AHSolidSnake/F-14A-Cockpit/Panels/Left Outboard/Back Spacer.stl

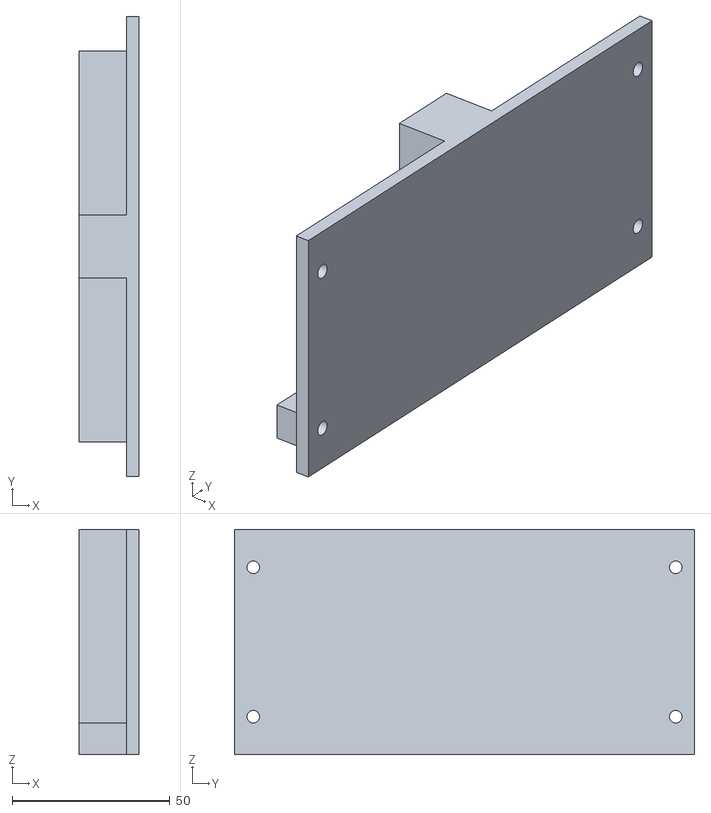
[picture p28: CAD file, 2025-07-25]
Panels/Left Outboard/Back Spacer.stl
19.0 x 146.0 x 71.4
