AHSolidSnake/F-14A-Cockpit/Panels/Left Outboard/ICS/ICS - Top Panel - Light.stl

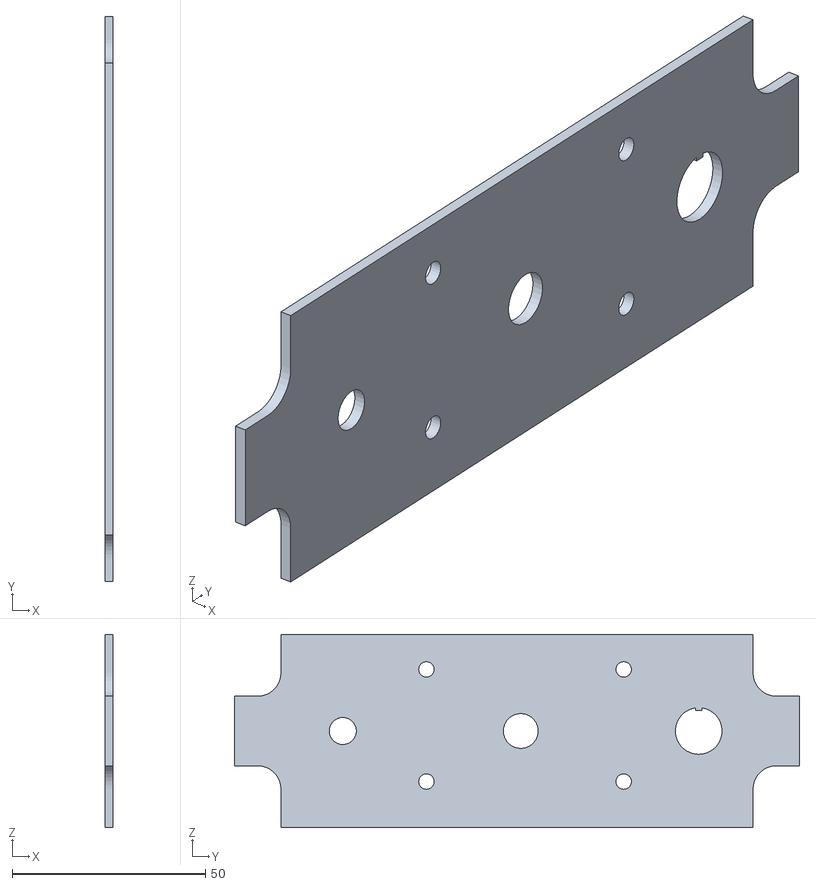
[picture p29: CAD file, 2025-02-26]
Panels/Left Outboard/ICS/ICS - Top Panel - Light.stl
2.00 x 146.1 x 50.0
