AHSolidSnake/F-14A-Cockpit/Panels/Left Outboard/THROTTLE/THROTTLE - Top Panel - Engrave.stl

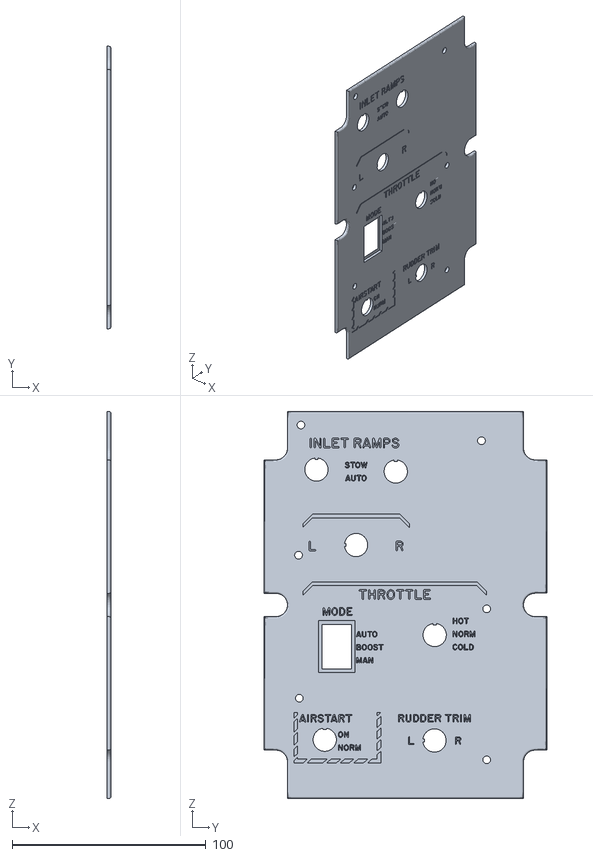
[picture p30: CAD file, 2025-02-26]
Panels/Left Outboard/THROTTLE/THROTTLE - Top Panel - Engrave.stl
2.00 x 146.0 x 200.0
