AHSolidSnake/F-14A-Cockpit/Panels/Left Outboard/VOLUME/VOLUME - Top Panel - Engrave.stl

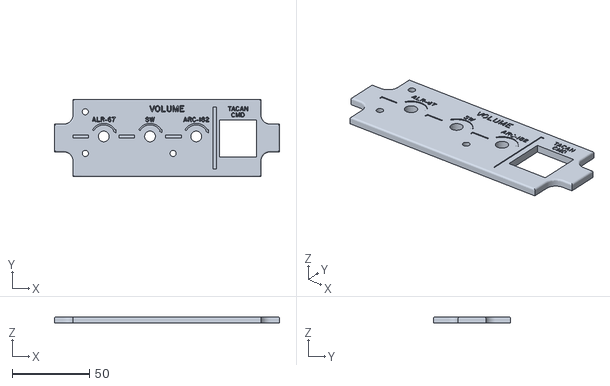
[picture p31: CAD file, 2025-06-24]
Panels/Left Outboard/VOLUME/VOLUME - Top Panel - Engrave.stl
146.0 x 50.0 x 4.00
