AHSolidSnake/F-14A-Cockpit/Panels/Left Vertical Panel/FUEL/FUEL - Top Panel - Light.stl

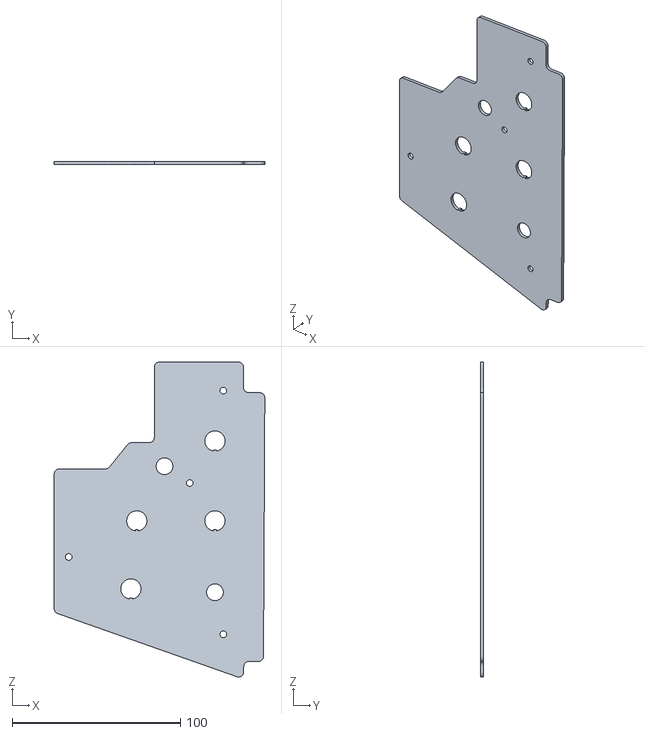
[picture p32: CAD file, 2025-03-23]
Panels/Left Vertical Panel/FUEL/FUEL - Top Panel - Light.stl
125.3 x 2.00 x 187.4
