AHSolidSnake/F-14A-Cockpit/Panels/Left Vertical Panel/GEAR/GEAR - Bottom Panel.stl

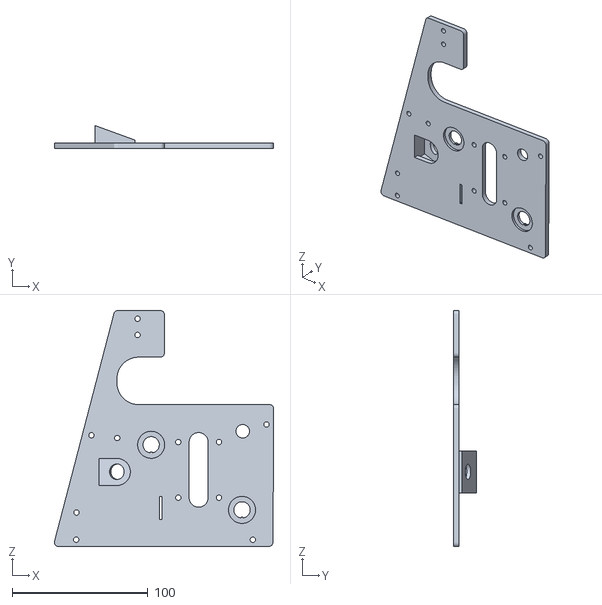
[picture p33: CAD file, 2025-06-24]
Panels/Left Vertical Panel/GEAR/GEAR - Bottom Panel.stl
161.7 x 16.9 x 174.0
