AHSolidSnake/F-14A-Cockpit/Panels/Left Vertical Panel/LAUNCH BAR/LAUNCH BAR - Top Panel - Engrave.stl

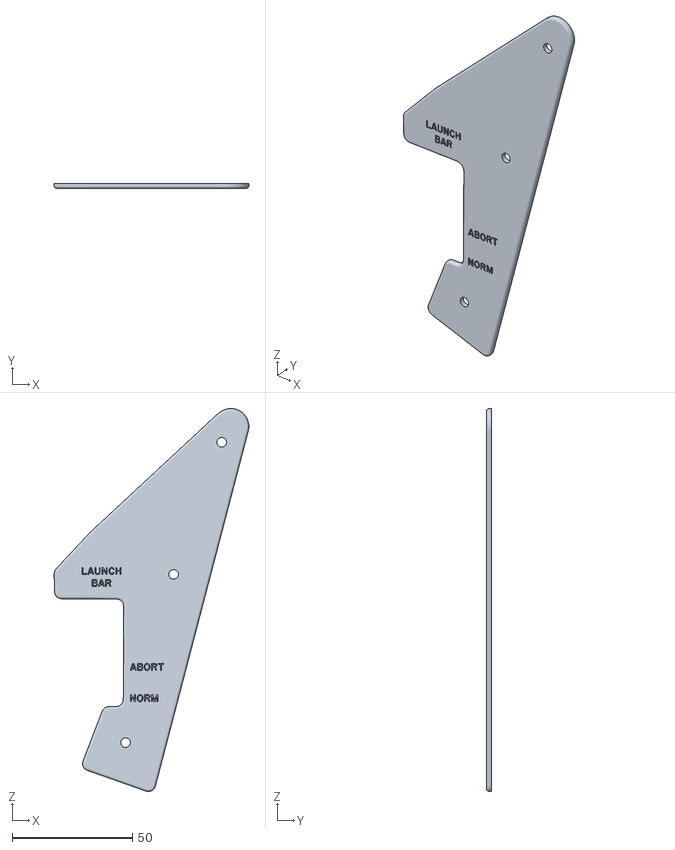
[picture p34: CAD file, 2025-03-22]
Panels/Left Vertical Panel/LAUNCH BAR/LAUNCH BAR - Top Panel - Engrave.stl
81.0 x 2.00 x 159.5
