AHSolidSnake/F-14A-Cockpit/Panels/Left Vertical Panel/LVP - Back Plate.stl

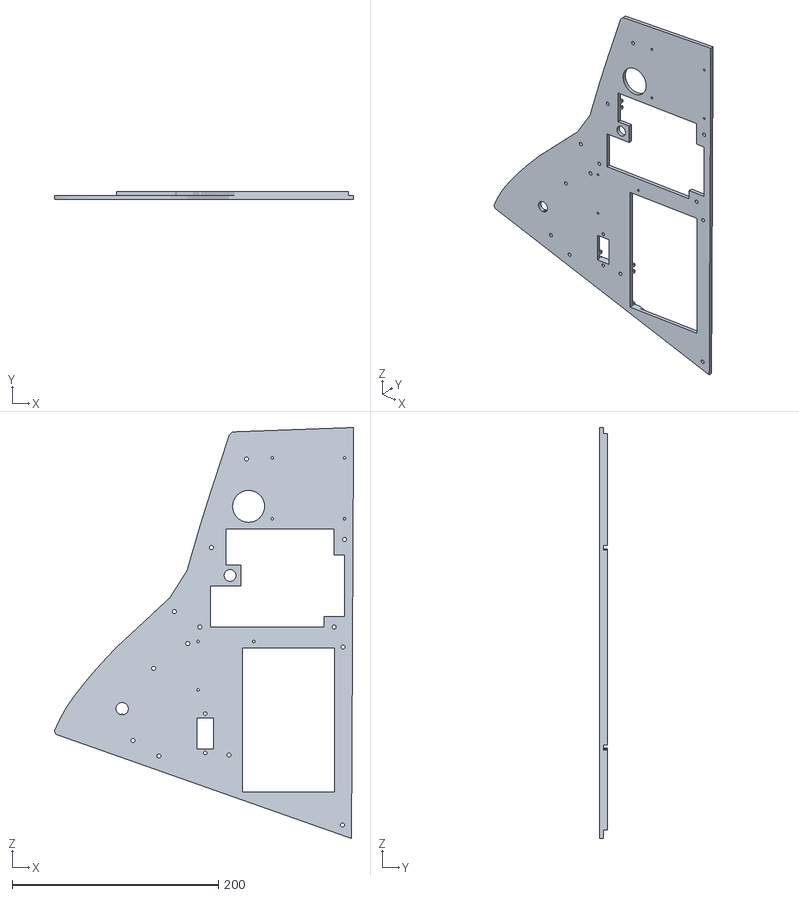
[picture p35: CAD file, 2025-03-16]
Panels/Left Vertical Panel/LVP - Back Plate.stl
290.1 x 8.00 x 398.5
