AHSolidSnake/F-14A-Cockpit/Panels/Right Inboard/AIRCON/AIRCON - Wheel.stl

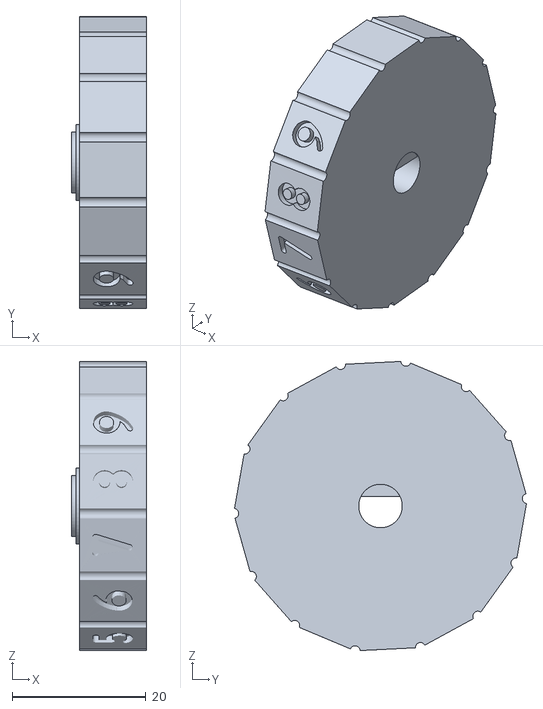
[picture p36: CAD file, 2025-06-24]
Panels/Right Inboard/AIRCON/AIRCON - Wheel.stl
11.2 x 43.7 x 43.3
