AHSolidSnake/F-14A-Cockpit/Panels/Right Inboard/C&W/C&W - Box.stl

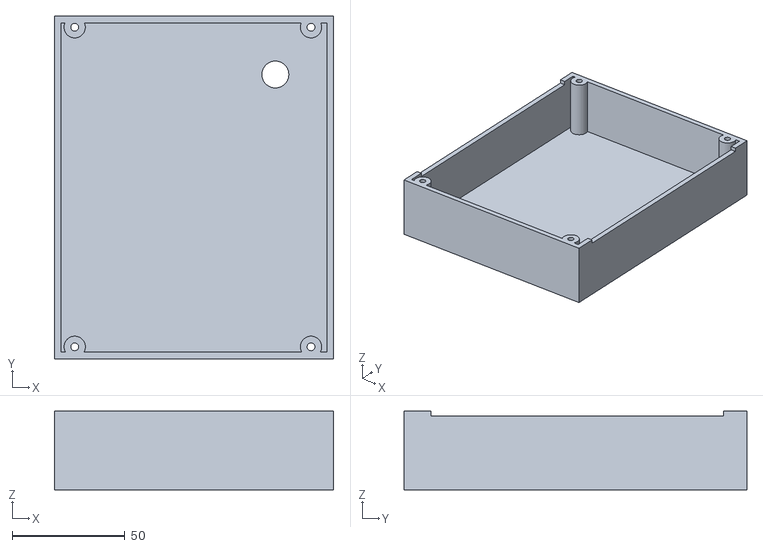
[picture p37: CAD file, 2025-05-10]
Panels/Right Inboard/C&W/C&W - Box.stl
124.0 x 152.4 x 35.0
