AHSolidSnake/F-14A-Cockpit/Panels/Right Inboard/EXTENV/EXTENV - Box.stl

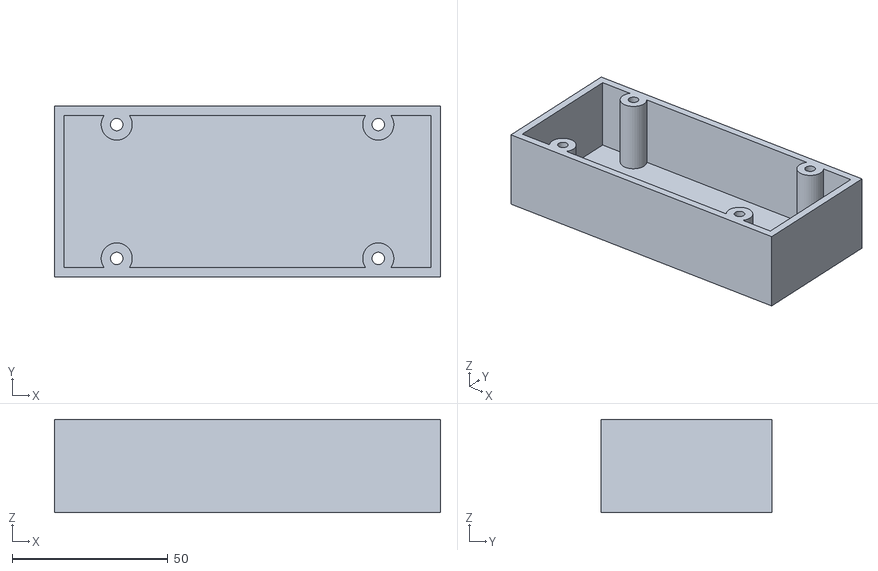
[picture p38: CAD file, 2025-04-17]
Panels/Right Inboard/EXTENV/EXTENV - Box.stl
124.0 x 55.0 x 30.0
