AHSolidSnake/F-14A-Cockpit/Panels/Right Inboard/HYD TRANS/HYD TRANS - Box.stl

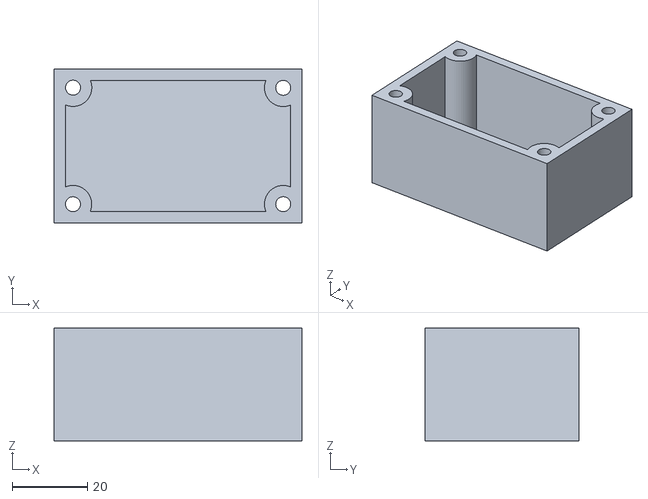
[picture p39: CAD file, 2025-04-17]
Panels/Right Inboard/HYD TRANS/HYD TRANS - Box.stl
66.0 x 41.0 x 30.0
