AHSolidSnake/F-14A-Cockpit/Panels/Right Inboard/MASTERGEN/MASTERGEN - Box.stl

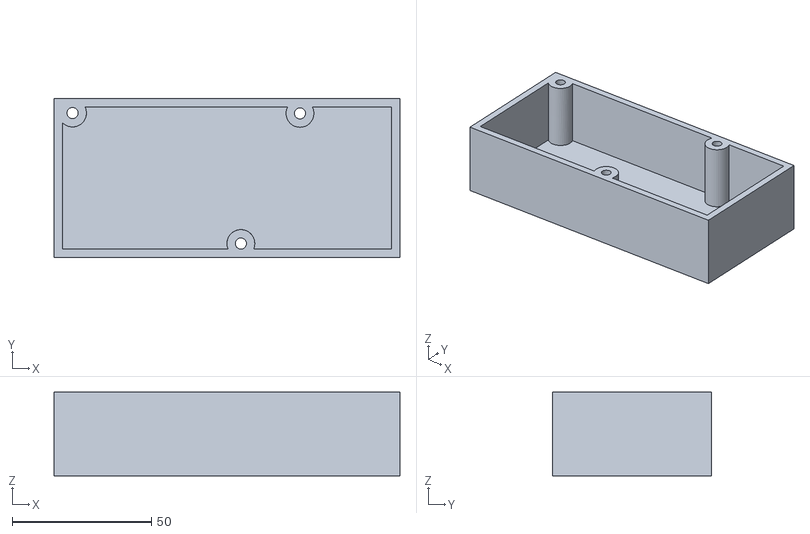
[picture p40: CAD file, 2025-04-17]
Panels/Right Inboard/MASTERGEN/MASTERGEN - Box.stl
124.1 x 57.0 x 30.0
