AHSolidSnake/F-14A-Cockpit/Panels/Right Inboard/SPOILERS/SPOILERS - Box.stl

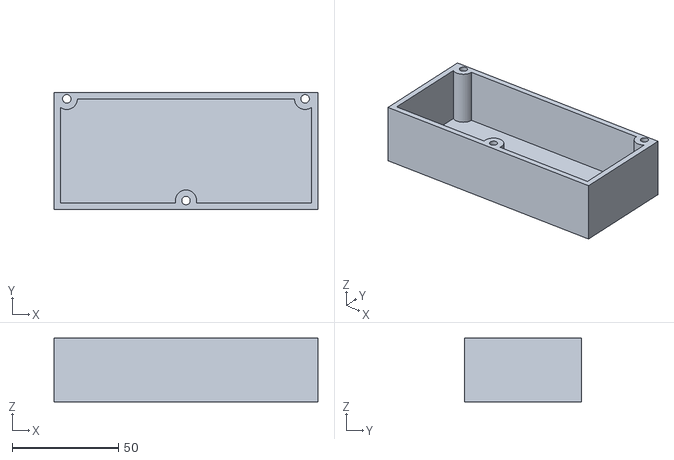
[picture p41: CAD file, 2025-04-13]
Panels/Right Inboard/SPOILERS/SPOILERS - Box.stl
124.1 x 55.0 x 30.0
