AHSolidSnake/F-14A-Cockpit/Panels/Right Instrument Panel/RIP - Back Plate.stl

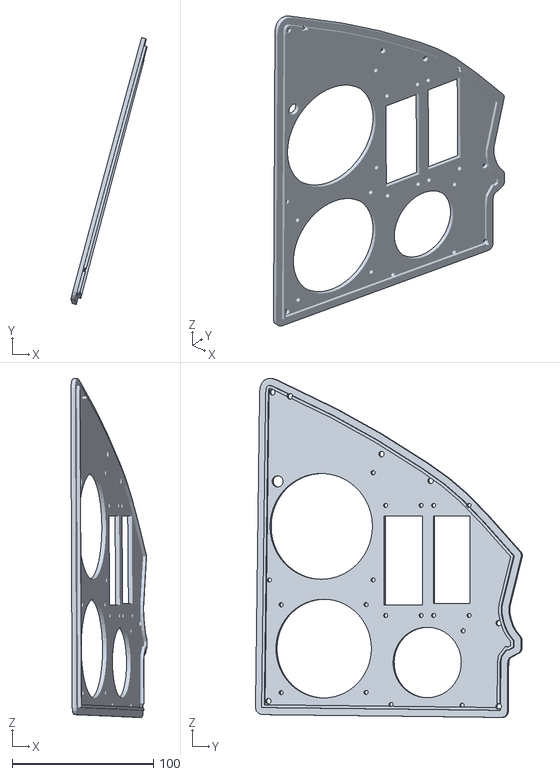
[picture p42: CAD file, 2025-03-30]
Panels/Right Instrument Panel/RIP - Back Plate.stl
54.2 x 189.3 x 240.3
