AHSolidSnake/F-14A-Cockpit/Panels/Right Outboard/COMPASS/COMPASS - Box.stl

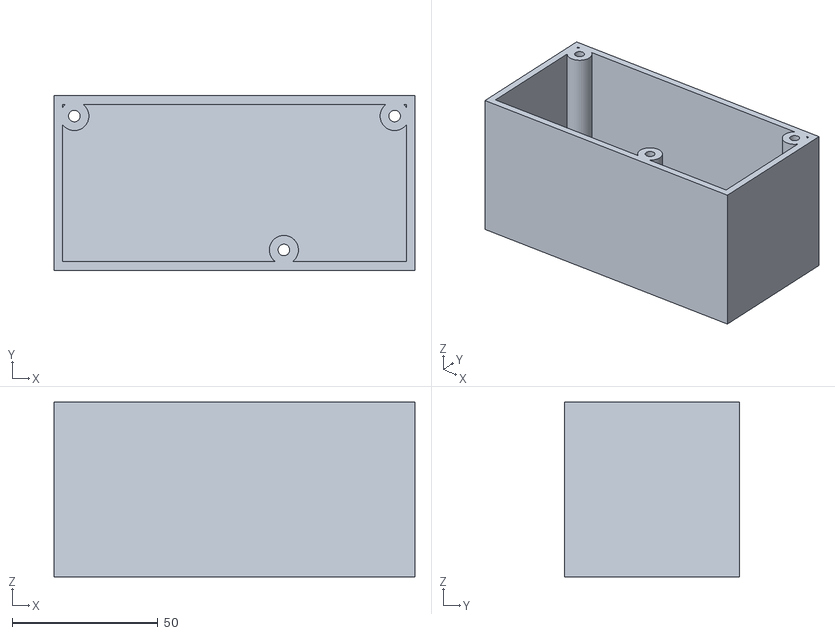
[picture p43: CAD file, 2025-03-30]
Panels/Right Outboard/COMPASS/COMPASS - Box.stl
124.1 x 60.0 x 60.0
