AHSolidSnake/F-14A-Cockpit/Panels/Right Outboard/ILS/ILS - Box.stl

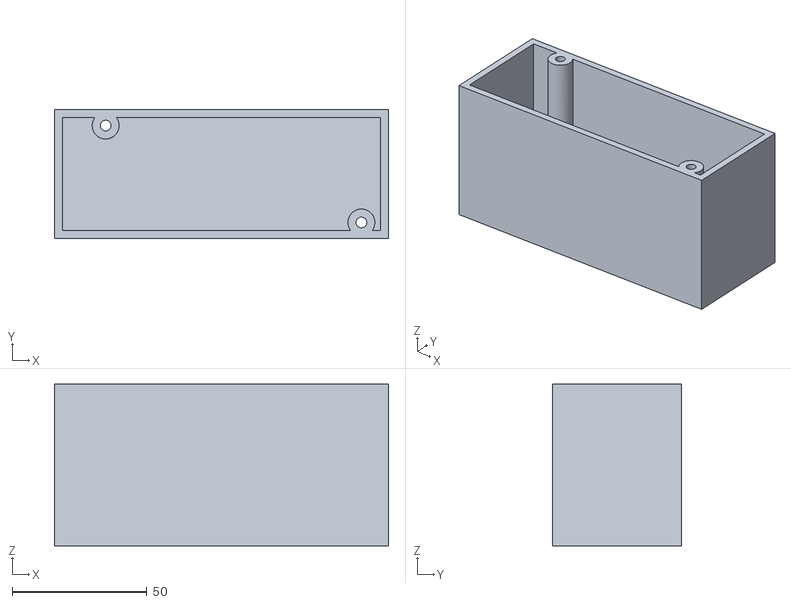
[picture p44: CAD file, 2025-03-30]
Panels/Right Outboard/ILS/ILS - Box.stl
124.1 x 48.0 x 60.0
