AHSolidSnake/F-14A-Cockpit/Panels/Right Outboard/MASTER LIGHTS/MASTER LIGHTS - Bottom Panel.stl

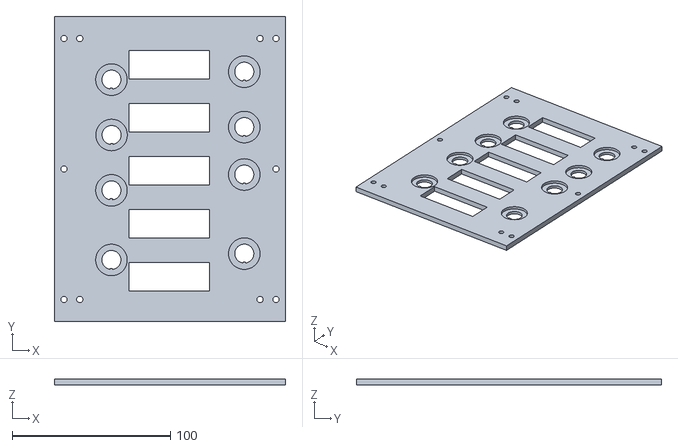
[picture p45: CAD file, 2025-04-11]
Panels/Right Outboard/MASTER LIGHTS/MASTER LIGHTS - Bottom Panel.stl
146.1 x 193.0 x 4.00
