AHSolidSnake/F-14A-Cockpit/Panels/Right Outboard/MASTER TEST/MASTER TEST - Bottom Panel.stl

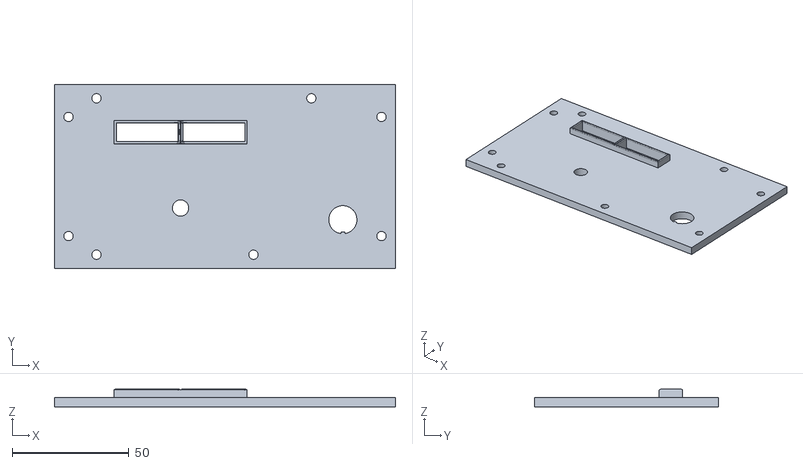
[picture p46: CAD file, 2025-03-30]
Panels/Right Outboard/MASTER TEST/MASTER TEST - Bottom Panel.stl
146.1 x 79.0 x 7.50
