AHSolidSnake/F-14A-Cockpit/Panels/Right Outboard/Spacer-OxygenFlow.stl

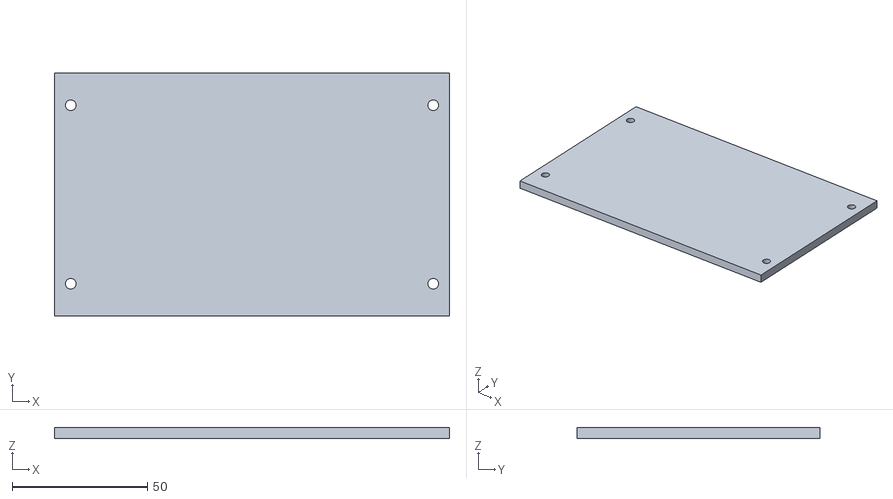
[picture p47: CAD file, 2025-03-22]
Panels/Right Outboard/Spacer-OxygenFlow.stl
146.1 x 90.0 x 4.00
