AHSolidSnake/F-14A-Cockpit/Panels/Right Sidewall/CANOPY/CANOPY - Box.stl

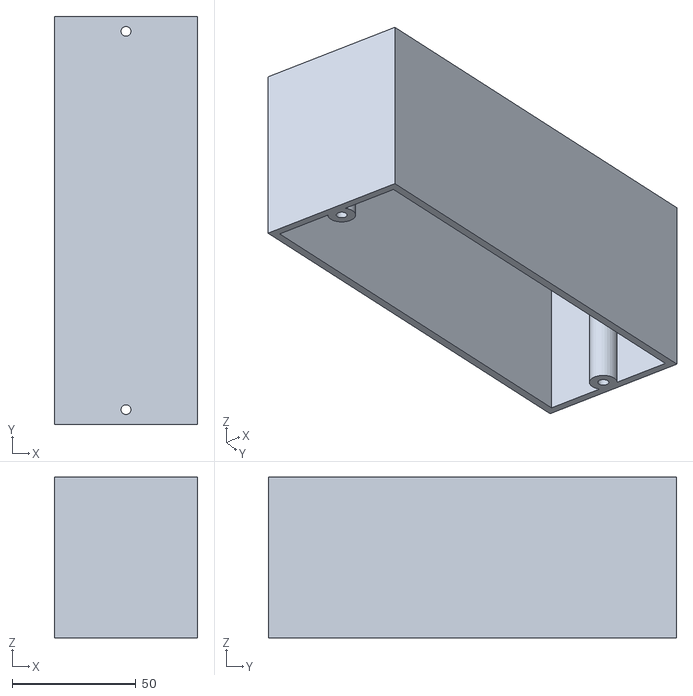
[picture p48: CAD file, 2025-06-24]
Panels/Right Sidewall/CANOPY/CANOPY - Box.stl
58.0 x 165.0 x 65.0
