AHSolidSnake/F-14A-Cockpit/Panels/Right Vertical Panel/HOOK/HOOK - Handle.stl

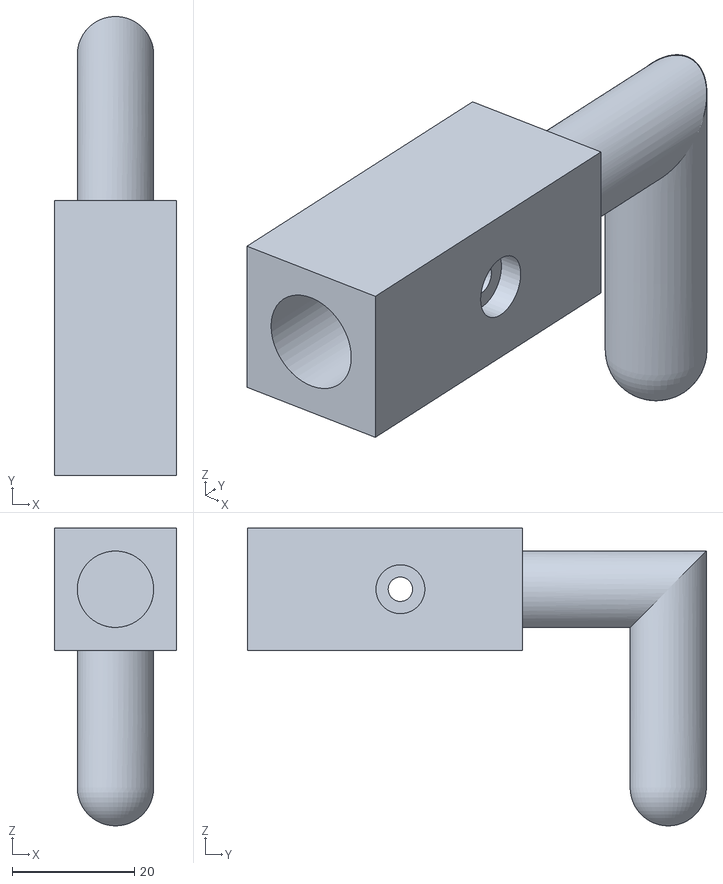
[picture p50: CAD file, 2025-06-24]
Panels/Right Vertical Panel/HOOK/HOOK - Handle.stl
20.0 x 75.0 x 48.7
