AHSolidSnake/F-14A-Cockpit/Panels/Right Vertical Panel/PDCP/PDCP - Top Panel - Engrave.stl

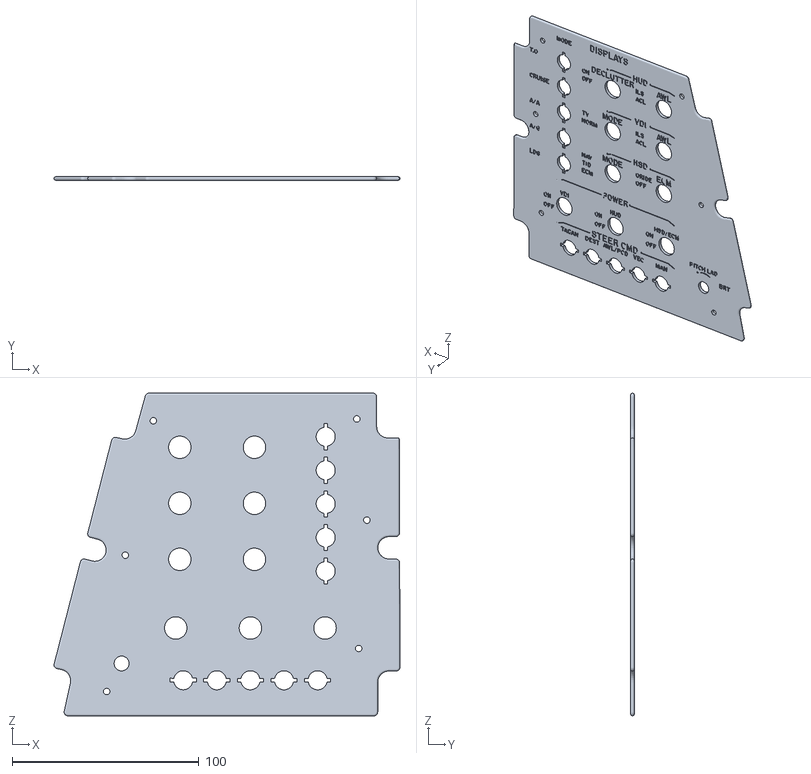
[picture p51: CAD file, 2025-04-07]
Panels/Right Vertical Panel/PDCP/PDCP - Top Panel - Engrave.stl
185.3 x 2.00 x 172.9
