AHSolidSnake/F-14A-Cockpit/Panels/Right Vertical Panel/RVP - Back Plate.stl

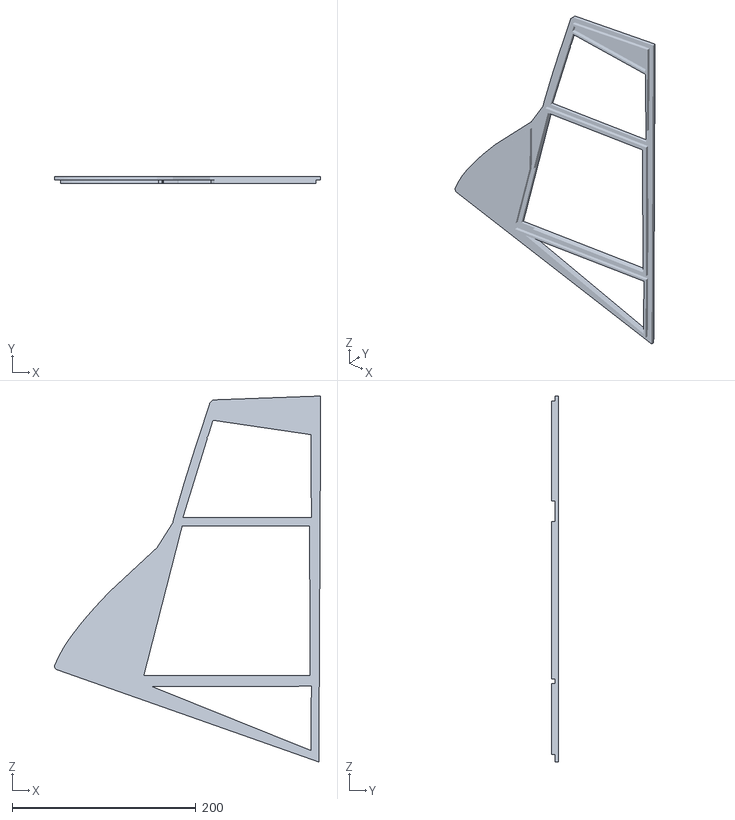
[picture p52: CAD file, 2025-03-15]
Panels/Right Vertical Panel/RVP - Back Plate.stl
290.1 x 8.00 x 398.5
