AHSolidSnake/F-14A-Cockpit/Panels/Support/Center Panel/ACM/ACM - Box - Top Left.stl

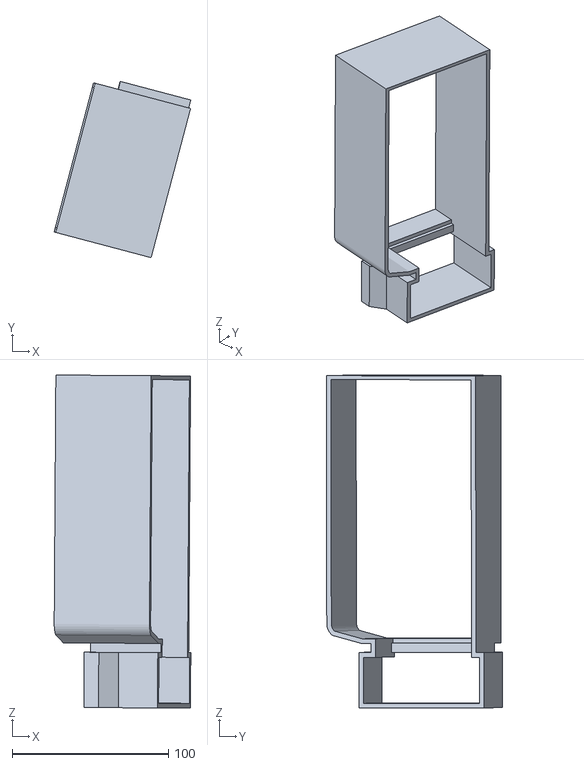
[picture p53: CAD file, 2025-03-09]
Panels/Support/Center Panel/ACM/ACM - Box - Top Left.stl
87.4 x 112.8 x 213.0
