AHSolidSnake/F-14A-Cockpit/Panels/Support/Center Panel/HSD/HSD - Box - Bottom.stl

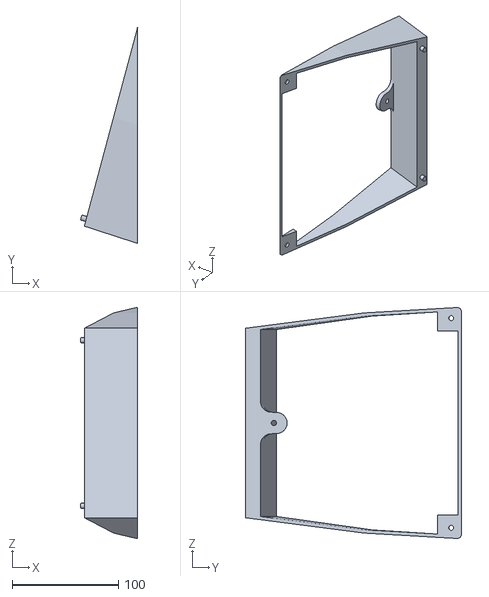
[picture p54: CAD file, 2025-03-30]
Panels/Support/Center Panel/HSD/HSD - Box - Bottom.stl
53.7 x 202.8 x 217.1
