AHSolidSnake/F-14A-Cockpit/Panels/Support/Center Panel/VDI/VDI - Box - Bottom.stl

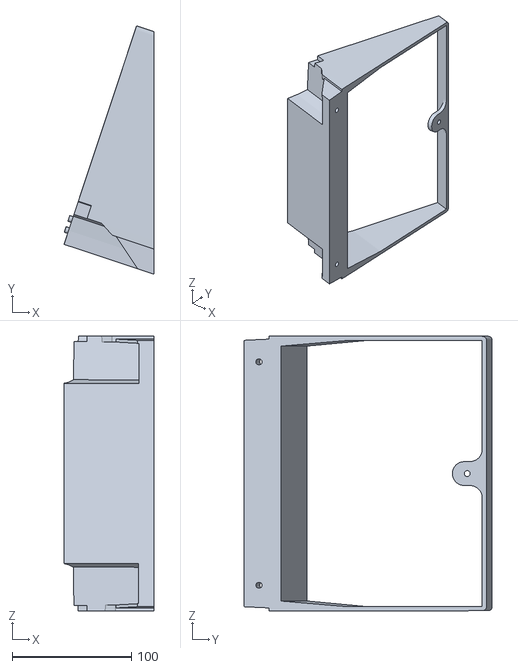
[picture p55: CAD file, 2025-03-29]
Panels/Support/Center Panel/VDI/VDI - Box - Bottom.stl
75.4 x 208.1 x 230.3
