AHSolidSnake/F-14A-Cockpit/Panels/Support/Left Vertical Panel/LVP - Box - Bottom.stl

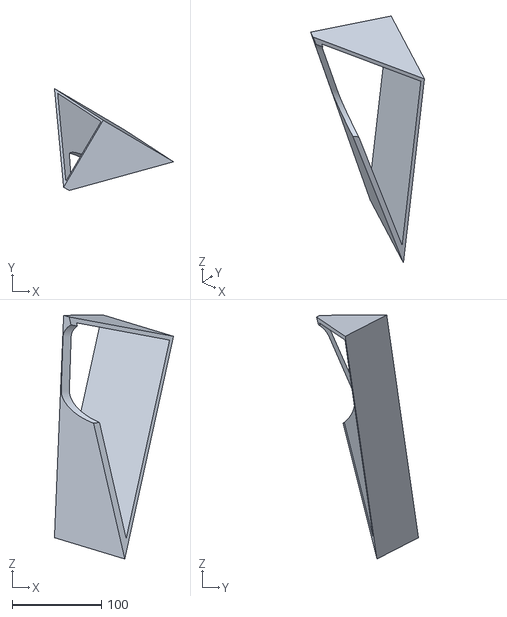
[picture p56: CAD file, 2025-03-30]
Panels/Support/Left Vertical Panel/LVP - Box - Bottom.stl
133.1 x 114.0 x 272.7
