AHSolidSnake/F-14A-Cockpit/Panels/Support/Right Vertical Panel/RVP - Box - Bottom.stl

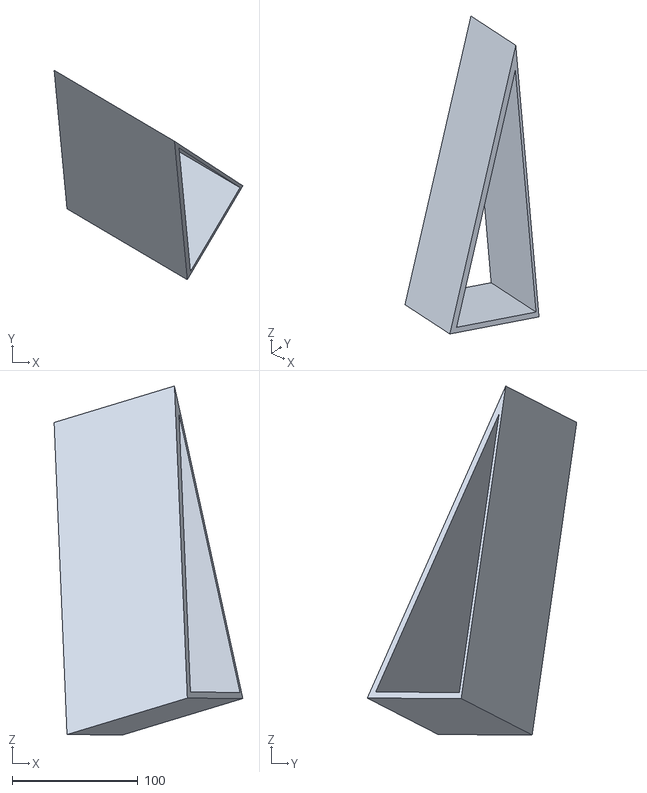
[picture p57: CAD file, 2025-03-30]
Panels/Support/Right Vertical Panel/RVP - Box - Bottom.stl
150.3 x 166.8 x 277.9
