AHSolidSnake/F-14A-Cockpit/Panels/Support/Side Panels/Left Middle Wedge.stl

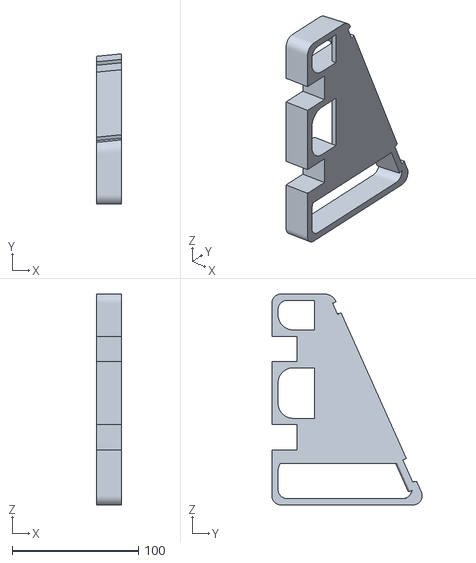
[picture p58: CAD file, 2025-06-24]
Panels/Support/Side Panels/Left Middle Wedge.stl
20.0 x 119.2 x 167.3
