AHSolidSnake/F-14A-Cockpit/Throttle/Base/Box/Back Plate Mount.stl

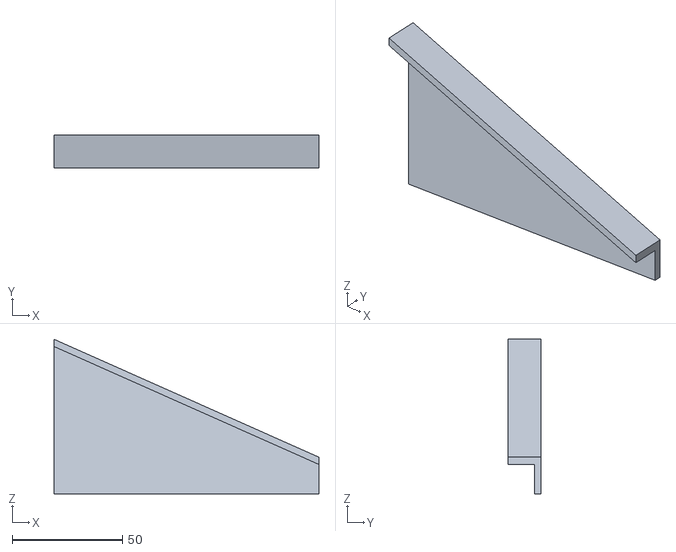
[picture p59: CAD file, 2025-06-24]
Throttle/Base/Box/Back Plate Mount.stl
120.1 x 15.0 x 70.0
