AHSolidSnake/F-14A-Cockpit/Throttle/Base/Flaps/Flaps Pot Mount.stl

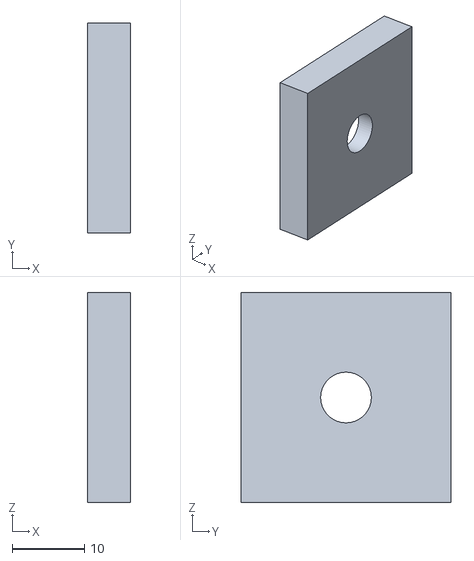
[picture p60: CAD file, 2025-06-24]
Throttle/Base/Flaps/Flaps Pot Mount.stl
6.00 x 29.0 x 29.0
