AHSolidSnake/F-14A-Cockpit/Throttle/Base/Throttle Base/Throttle Levers Left Plate.stl

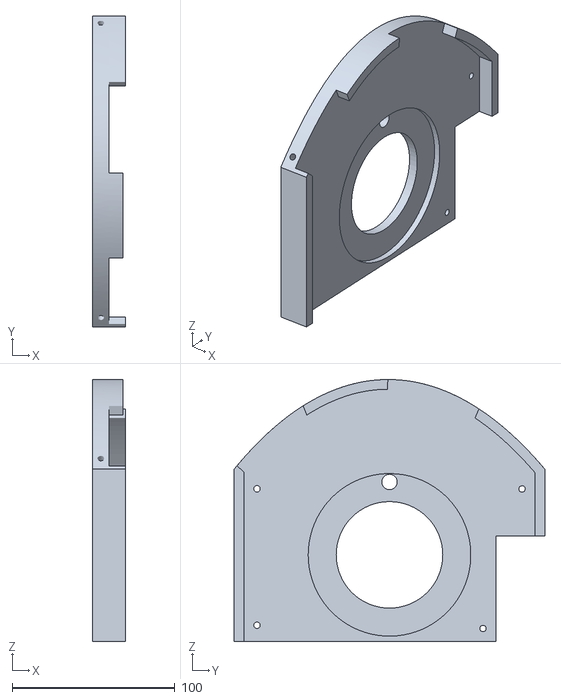
[picture p61: CAD file, 2025-06-24]
Throttle/Base/Throttle Base/Throttle Levers Left Plate.stl
20.0 x 191.0 x 161.1
