AHSolidSnake/F-14A-Cockpit/Throttle/Base/Wing Sweep/Mechanism.stl

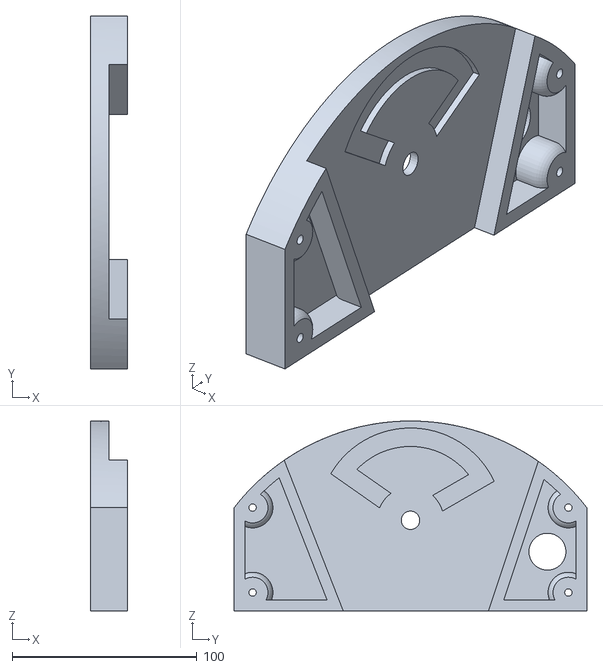
[picture p62: CAD file, 2025-06-24]
Throttle/Base/Wing Sweep/Mechanism.stl
20.0 x 191.0 x 102.9
