AHSolidSnake/F-14A-Cockpit/Throttle/Grips/Levers/Right Arm.stl

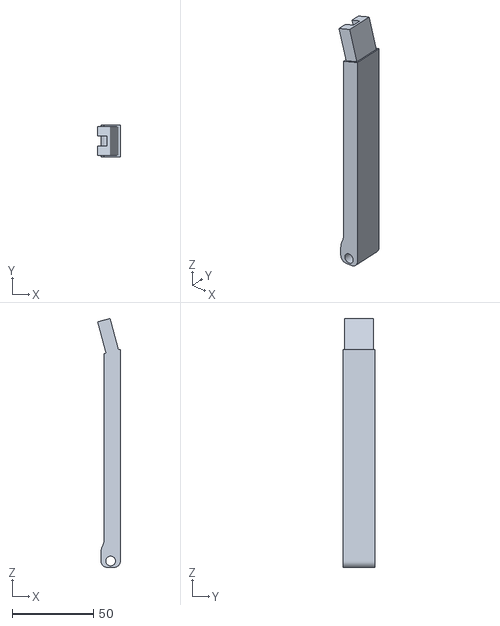
[picture p63: CAD file, 2025-06-24]
Throttle/Grips/Levers/Right Arm.stl
14.1 x 20.0 x 153.7
