AHSolidSnake/F-14A-Cockpit/Extras/Drill Guide.stl

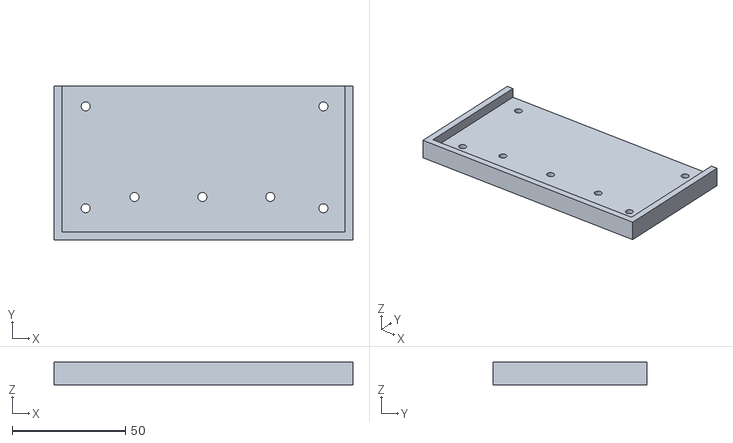
[picture p64: CAD file, 2025-04-07]
Extras/Drill Guide.stl
132.1 x 68.0 x 10.0
