AHSolidSnake/F-14A-Cockpit/Panels/Center Panel/ACM/ACM - AoA/ACM - AoA - Back Plate.stl

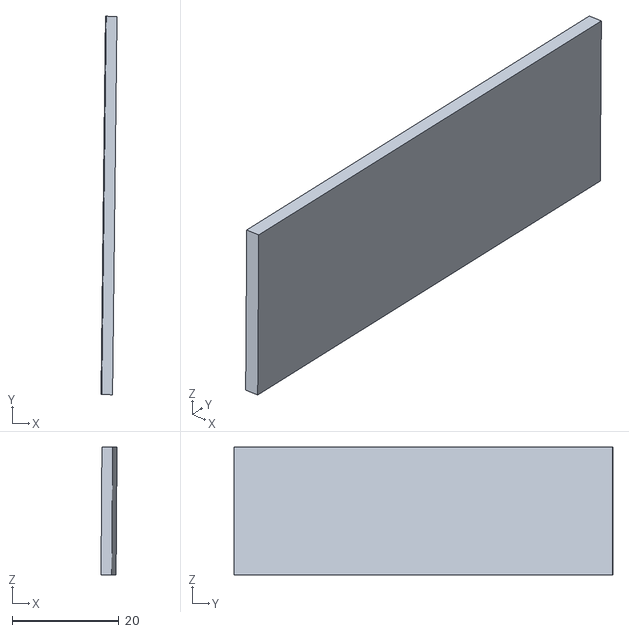
[picture p65: CAD file, 2025-03-23]
Panels/Center Panel/ACM/ACM - AoA/ACM - AoA - Back Plate.stl
3.02 x 71.0 x 24.0
