AHSolidSnake/F-14A-Cockpit/Panels/Center Panel/ACM/ACM - Lights/ACM - Lights - Collision Light.stl

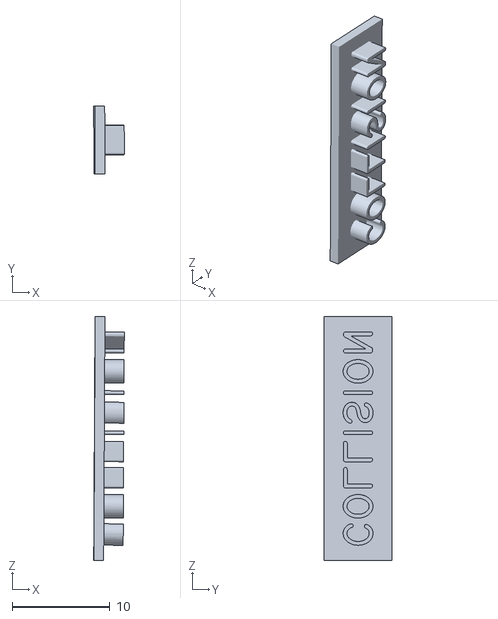
[picture p66: CAD file, 2025-03-16]
Panels/Center Panel/ACM/ACM - Lights/ACM - Lights - Collision Light.stl
3.14 x 7.00 x 25.0
