AHSolidSnake/F-14A-Cockpit/Panels/Center Panel/ACM/ACM - Master Arm - Cover.stl

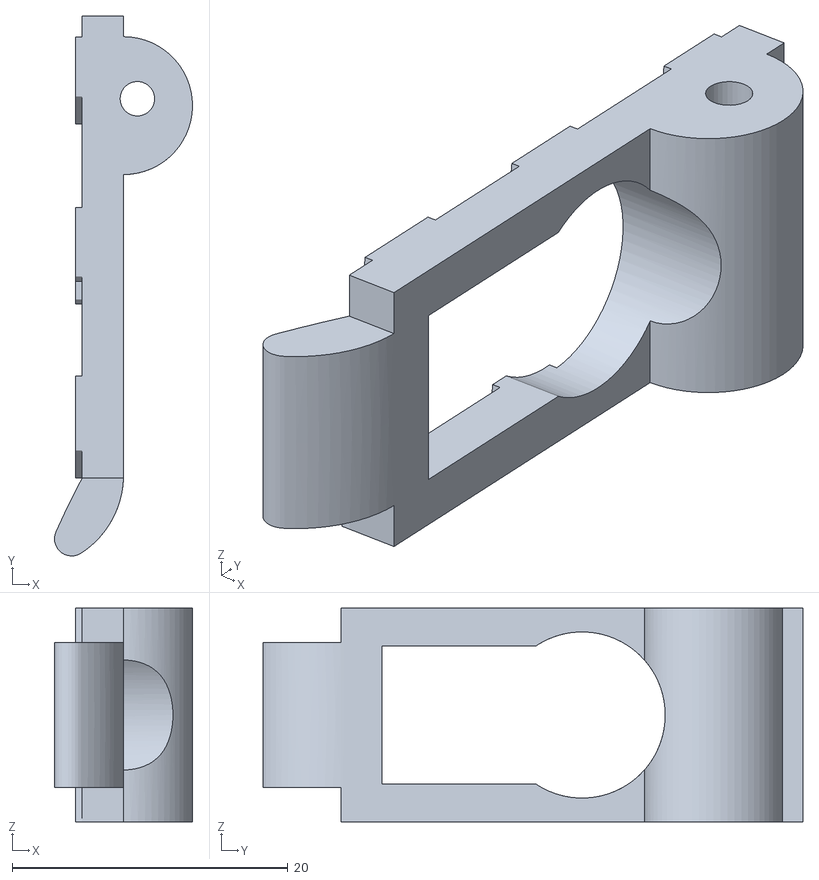
[picture p67: CAD file, 2025-03-16]
Panels/Center Panel/ACM/ACM - Master Arm - Cover.stl
10.0 x 39.2 x 15.5
