AHSolidSnake/F-14A-Cockpit/Panels/Center Panel/ACM/ACM - Turn Slip/ACM - Turn Slip - Engrave.stl

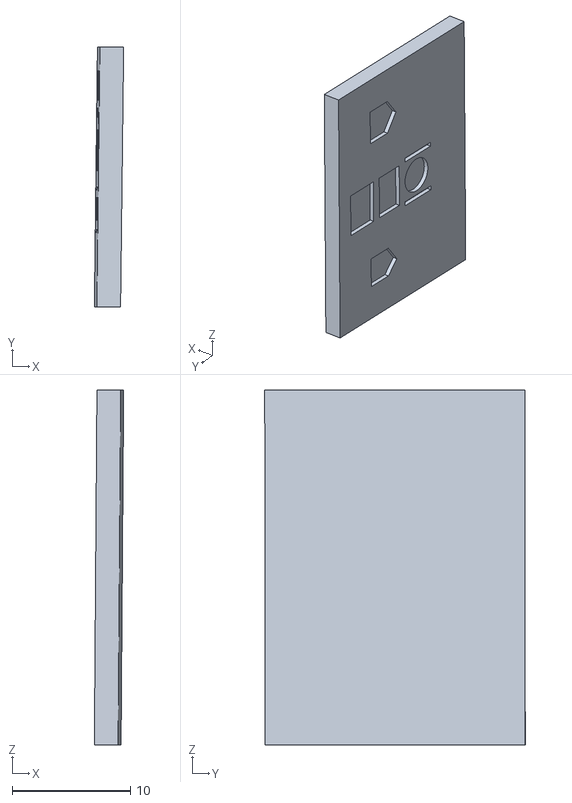
[picture p68: CAD file, 2025-03-23]
Panels/Center Panel/ACM/ACM - Turn Slip/ACM - Turn Slip - Engrave.stl
2.48 x 22.0 x 30.0
