AHSolidSnake/F-14A-Cockpit/Panels/Center Panel/HSD/HSD - Top Panel - Left Engrave.stl

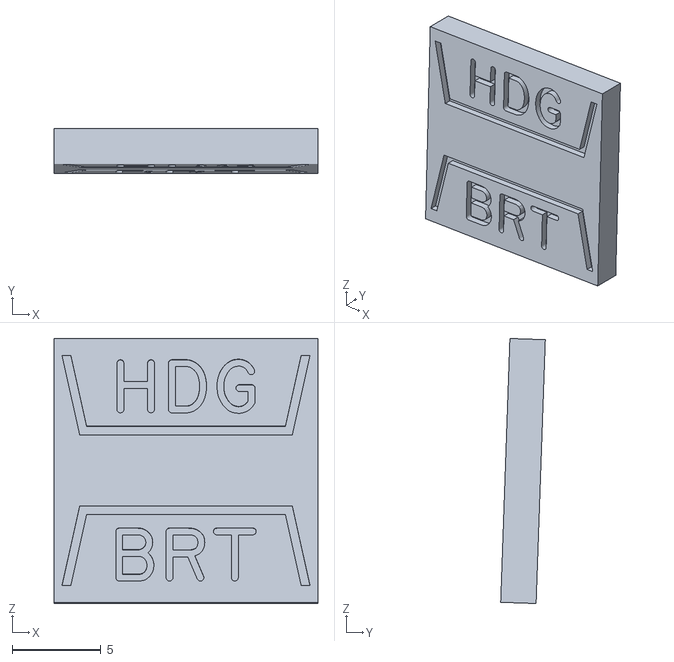
[picture p69: CAD file, 2025-05-10]
Panels/Center Panel/HSD/HSD - Top Panel - Left Engrave.stl
14.9 x 2.52 x 15.0
