AHSolidSnake/F-14A-Cockpit/Panels/Center Panel/VDI/VDI - Top Panel - Light.stl

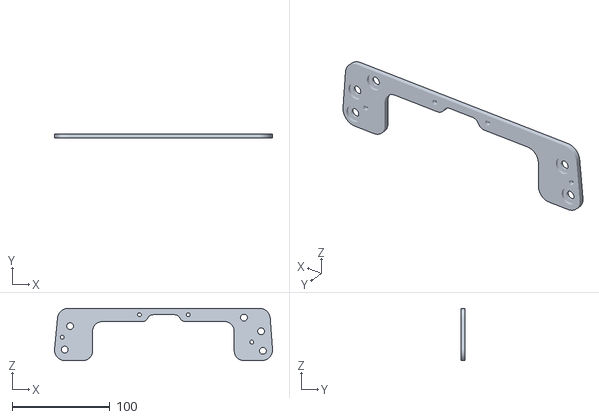
[picture p70: CAD file, 2025-03-30]
Panels/Center Panel/VDI/VDI - Top Panel - Light.stl
223.2 x 4.00 x 53.7
