AHSolidSnake/F-14A-Cockpit/Panels/Left Inboard/ARC-159/ARC-159 - Freq Chart.stl

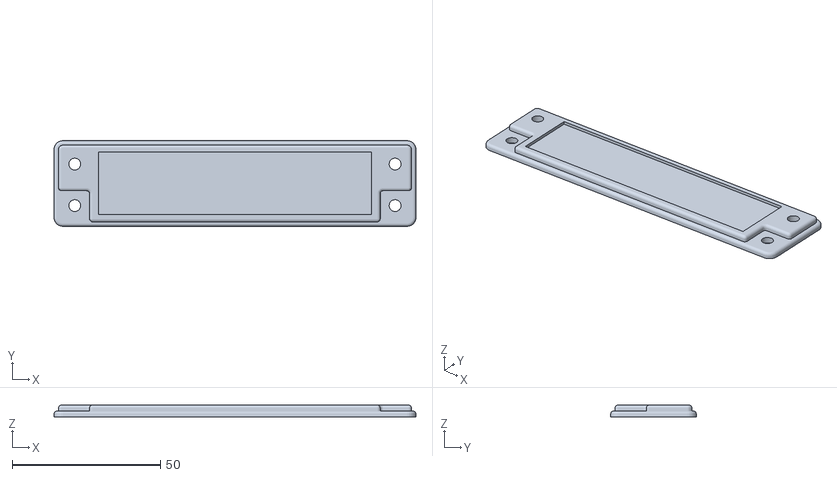
[picture p71: CAD file, 2025-07-18]
Panels/Left Inboard/ARC-159/ARC-159 - Freq Chart.stl
122.1 x 28.9 x 4.00
