AHSolidSnake/F-14A-Cockpit/Panels/Left Inboard/TACAN/TACAN - Box.stl

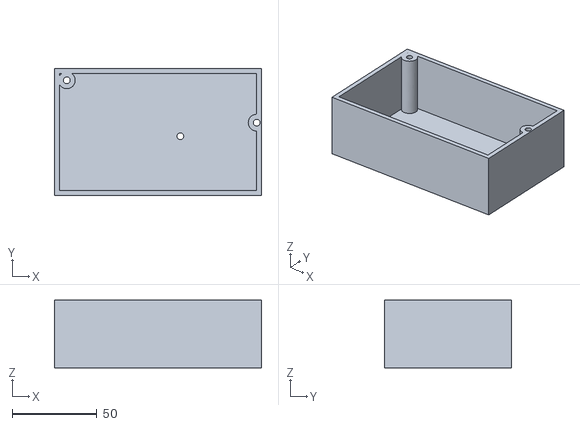
[picture p72: CAD file, 2025-07-25]
Panels/Left Inboard/TACAN/TACAN - Box.stl
122.1 x 75.0 x 40.0
