AHSolidSnake/F-14A-Cockpit/Panels/Left Instrument Panel/Checklist - Back Panel.stl

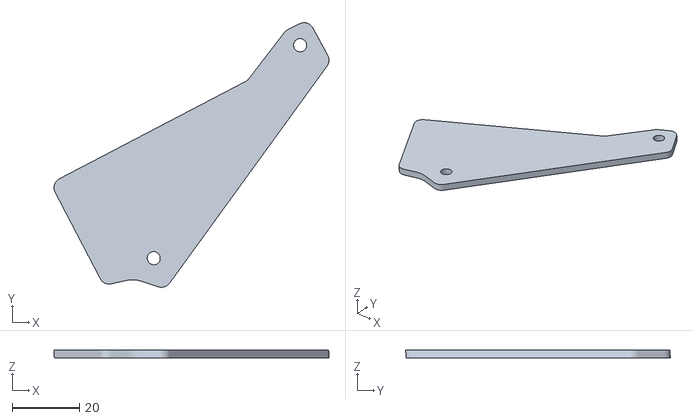
[picture p73: CAD file, 2025-03-30]
Panels/Left Instrument Panel/Checklist - Back Panel.stl
82.0 x 78.9 x 2.31
