AHSolidSnake/F-14A-Cockpit/Panels/Left Outboard/ASYM LIMIT/ASYM LIMIT - Top Panel - Engrave.stl

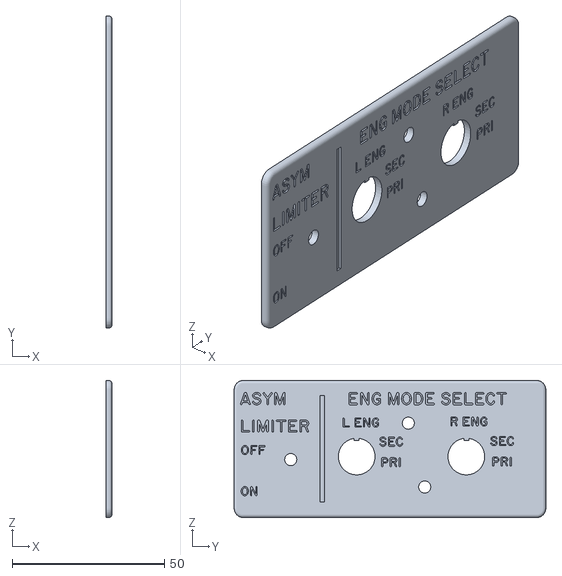
[picture p74: CAD file, 2025-02-26]
Panels/Left Outboard/ASYM LIMIT/ASYM LIMIT - Top Panel - Engrave.stl
2.00 x 102.4 x 45.0
