AHSolidSnake/F-14A-Cockpit/Panels/Left Outboard/VOLUME/VOLUME - Top Panel - Light.stl

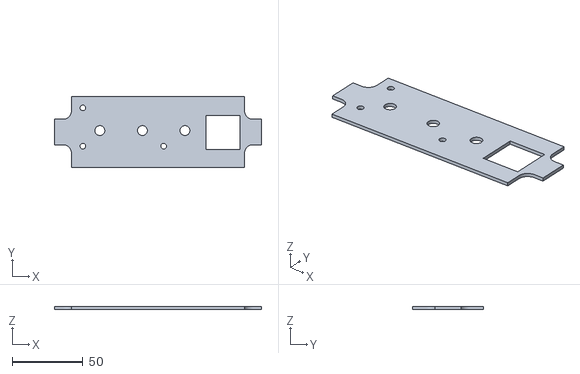
[picture p75: CAD file, 2025-02-26]
Panels/Left Outboard/VOLUME/VOLUME - Top Panel - Light.stl
146.0 x 50.0 x 2.00
