AHSolidSnake/F-14A-Cockpit/Panels/Left Vertical Panel/GEAR/GEAR - Top Panel - Light.stl

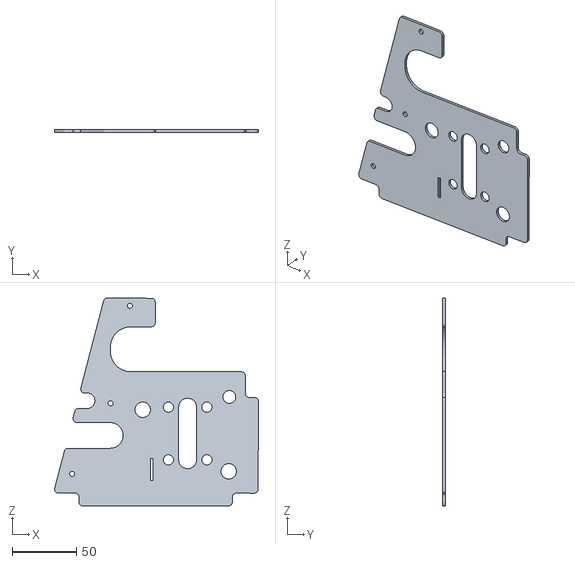
[picture p77: CAD file, 2025-06-24]
Panels/Left Vertical Panel/GEAR/GEAR - Top Panel - Light.stl
159.0 x 2.00 x 162.0
