AHSolidSnake/F-14A-Cockpit/Panels/Right Inboard/AIRCON/AIRCON - Bottom Panel.stl

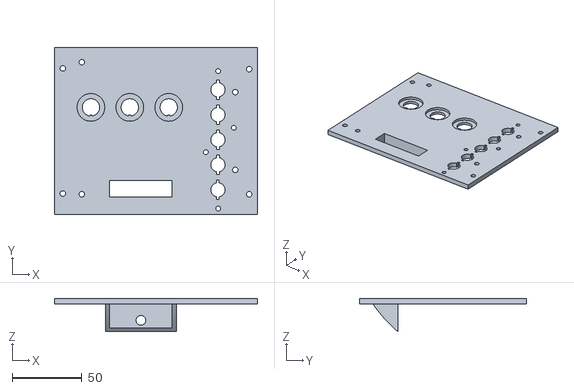
[picture p78: CAD file, 2025-06-24]
Panels/Right Inboard/AIRCON/AIRCON - Bottom Panel.stl
146.1 x 120.0 x 24.0
