AHSolidSnake/F-14A-Cockpit/Panels/Right Inboard/C&W/C&W - Light Box.stl

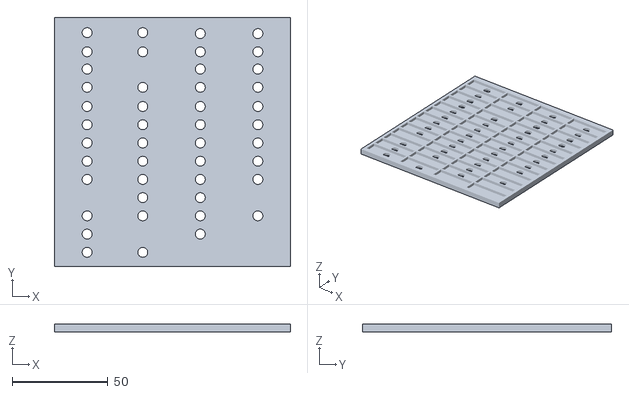
[picture p79: CAD file, 2025-04-07]
Panels/Right Inboard/C&W/C&W - Light Box.stl
123.0 x 130.0 x 4.00
