AHSolidSnake/F-14A-Cockpit/Panels/Right Inboard/EXTENV/EXTENV - Top Panel.stl

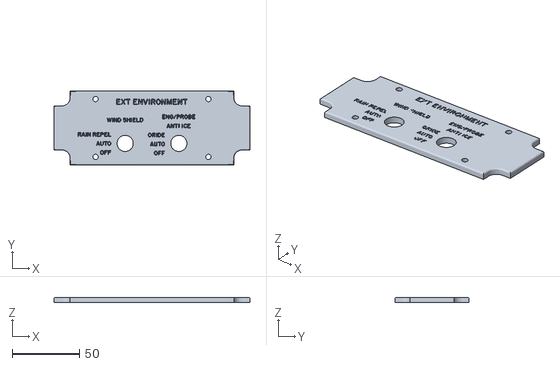
[picture p80: CAD file, 2025-04-13]
Panels/Right Inboard/EXTENV/EXTENV - Top Panel.stl
146.0 x 55.0 x 4.00
