AHSolidSnake/F-14A-Cockpit/Panels/Right Inboard/HYD TRANS/HYD TRANS - Bottom Panel.stl

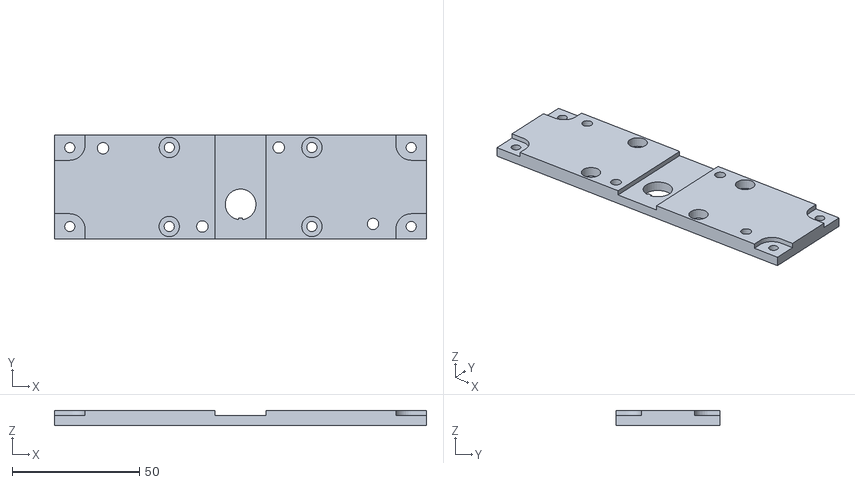
[picture p81: CAD file, 2025-04-13]
Panels/Right Inboard/HYD TRANS/HYD TRANS - Bottom Panel.stl
146.0 x 41.0 x 6.00
