AHSolidSnake/F-14A-Cockpit/Panels/Right Inboard/MASTERGEN/MASTERGEN - Bottom Panel.stl

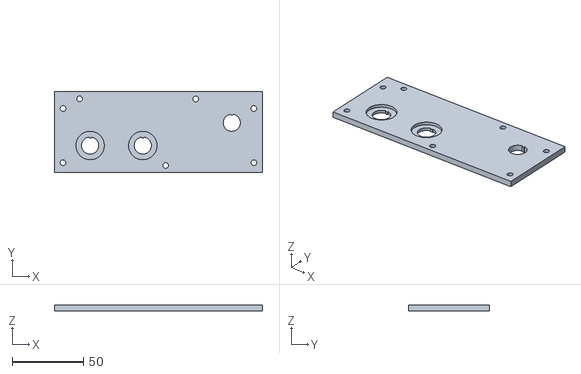
[picture p82: CAD file, 2025-03-30]
Panels/Right Inboard/MASTERGEN/MASTERGEN - Bottom Panel.stl
146.1 x 57.0 x 4.00
