AHSolidSnake/F-14A-Cockpit/Panels/Right Inboard/SPOILERS/SPOILERS - Top Panel - Engrave.stl

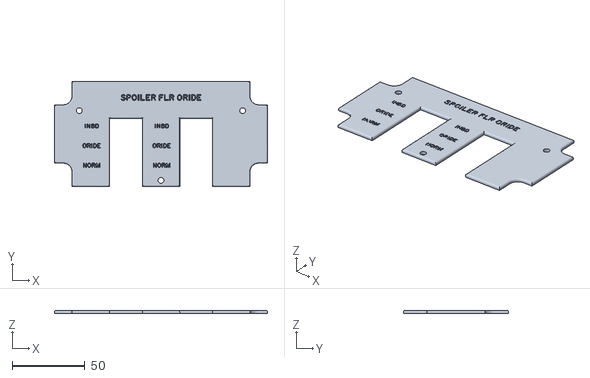
[picture p83: CAD file, 2025-04-07]
Panels/Right Inboard/SPOILERS/SPOILERS - Top Panel - Engrave.stl
146.1 x 72.0 x 2.00
