AHSolidSnake/F-14A-Cockpit/Panels/Right Instrument Panel/Landing checklist.stl

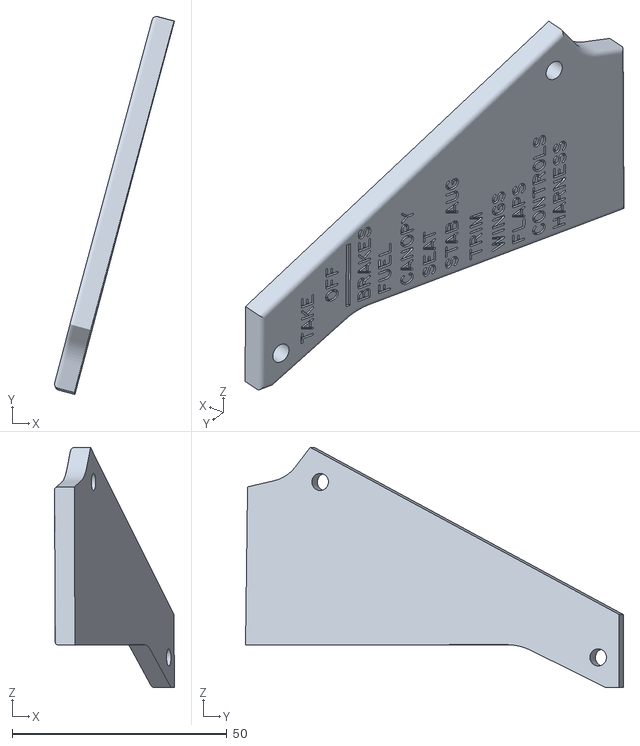
[picture p84: CAD file, 2025-03-30]
Panels/Right Instrument Panel/Landing checklist.stl
27.9 x 88.0 x 55.9
