AHSolidSnake/F-14A-Cockpit/Panels/Right Outboard/COMPASS/COMPASS - Bottom Panel.stl

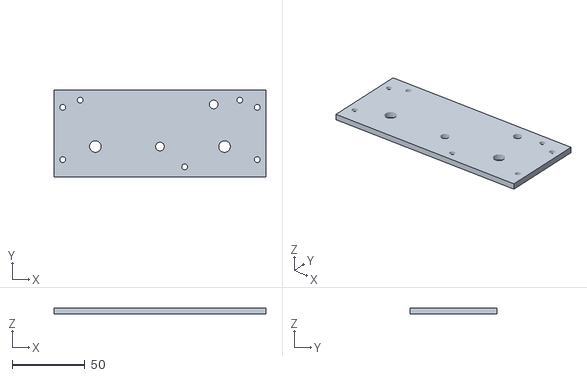
[picture p85: CAD file, 2025-03-30]
Panels/Right Outboard/COMPASS/COMPASS - Bottom Panel.stl
146.1 x 60.0 x 4.00
