AHSolidSnake/F-14A-Cockpit/Panels/Right Outboard/ILS/ILS - Bottom Panel.stl

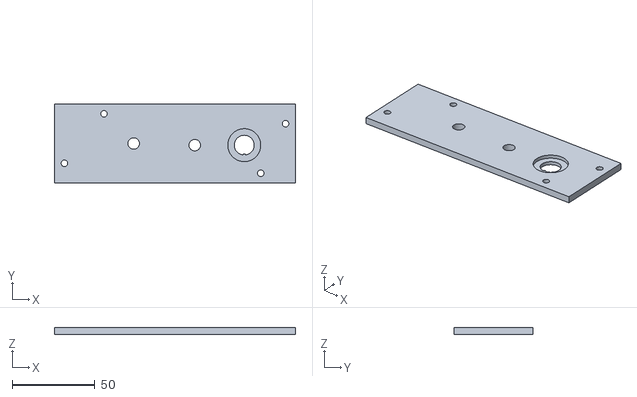
[picture p86: CAD file, 2025-03-30]
Panels/Right Outboard/ILS/ILS - Bottom Panel.stl
146.1 x 48.0 x 4.00
