AHSolidSnake/F-14A-Cockpit/Panels/Right Outboard/MASTER LIGHTS/MASTER LIGHTS - Box.stl

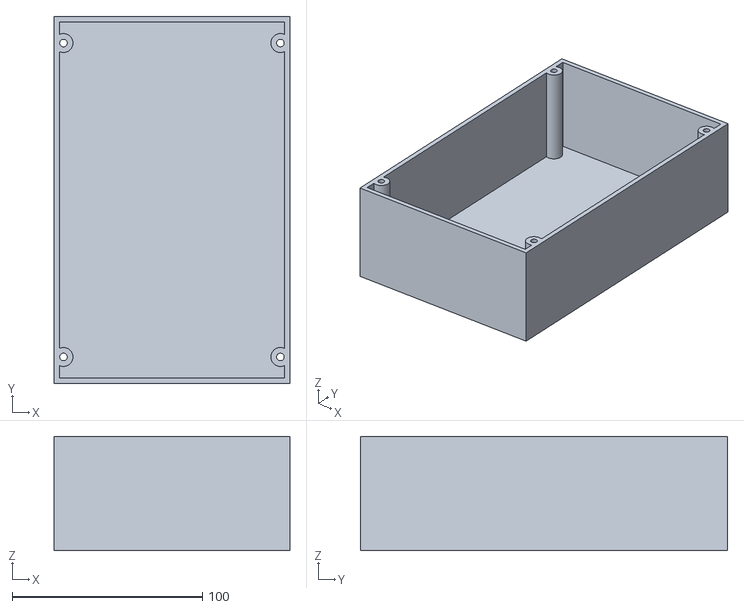
[picture p87: CAD file, 2025-03-30]
Panels/Right Outboard/MASTER LIGHTS/MASTER LIGHTS - Box.stl
124.1 x 193.0 x 60.0
