AHSolidSnake/F-14A-Cockpit/Panels/Right Outboard/MASTER TEST/MASTER TEST - Top Panel.stl

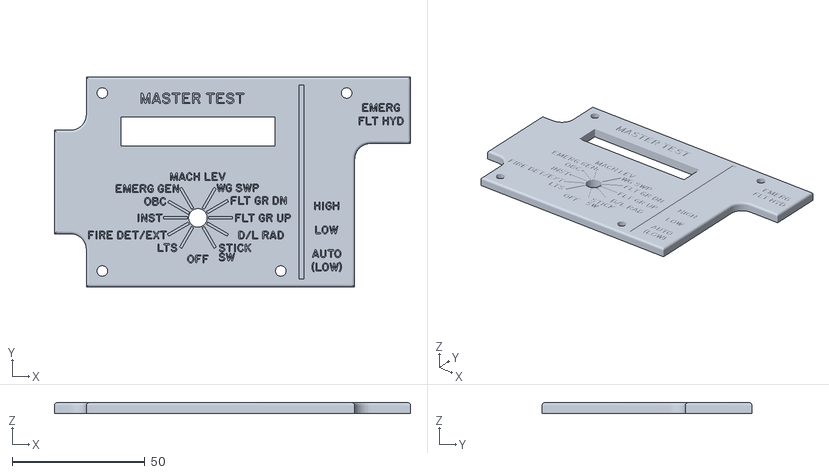
[picture p88: CAD file, 2025-03-30]
Panels/Right Outboard/MASTER TEST/MASTER TEST - Top Panel.stl
134.1 x 79.0 x 4.00
