AHSolidSnake/F-14A-Cockpit/Panels/Right Sidewall/CANOPY/CANOPY - Mouse Mount.stl

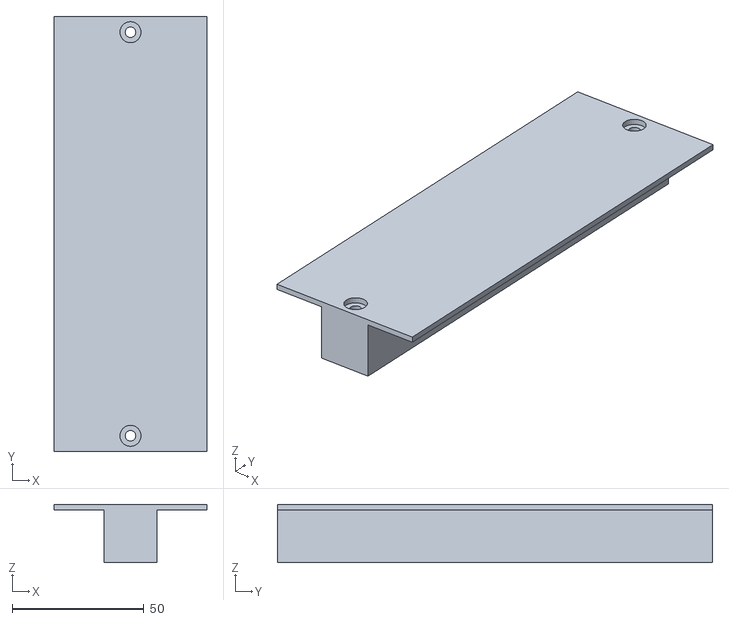
[picture p89: CAD file, 2025-06-24]
Panels/Right Sidewall/CANOPY/CANOPY - Mouse Mount.stl
58.0 x 165.0 x 22.0
