AHSolidSnake/F-14A-Cockpit/Panels/Right Vertical Panel/ELEV LEAD/ELEV LEAD - Top Panel - Engrave.stl

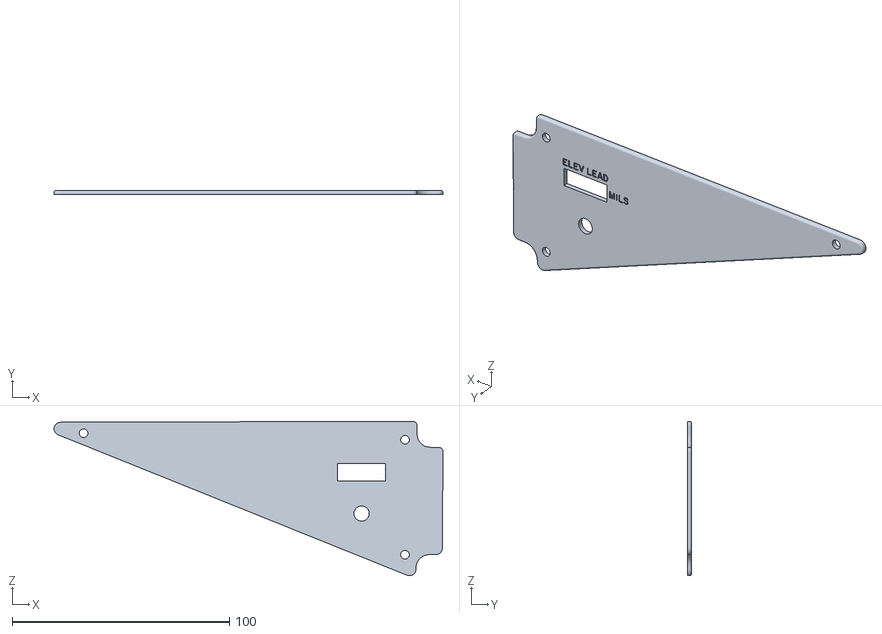
[picture p90: CAD file, 2025-04-11]
Panels/Right Vertical Panel/ELEV LEAD/ELEV LEAD - Top Panel - Engrave.stl
179.1 x 2.00 x 71.1
