AHSolidSnake/F-14A-Cockpit/Panels/Right Vertical Panel/HOOK/HOOK - Top Panel - Engrave.stl

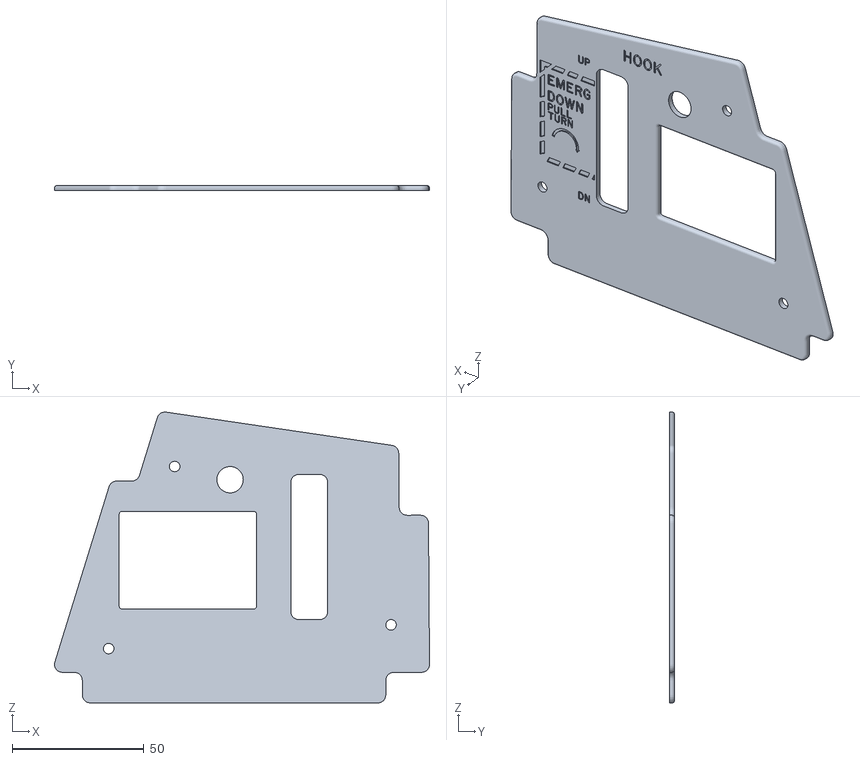
[picture p91: CAD file, 2025-04-29]
Panels/Right Vertical Panel/HOOK/HOOK - Top Panel - Engrave.stl
142.1 x 2.00 x 110.2
