AHSolidSnake/F-14A-Cockpit/Panels/Right Vertical Panel/JETT Cover.stl

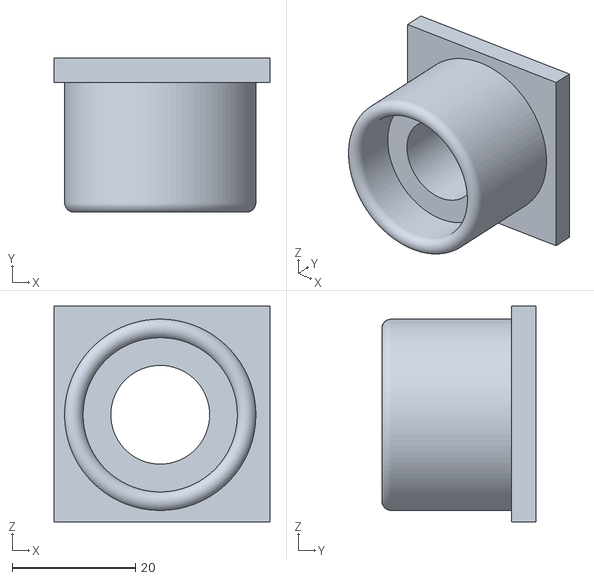
[picture p92: CAD file, 2025-03-15]
Panels/Right Vertical Panel/JETT Cover.stl
35.0 x 25.0 x 35.0
