AHSolidSnake/F-14A-Cockpit/Panels/Right Vertical Panel/PDCP/PDCP - Bottom Panel.stl

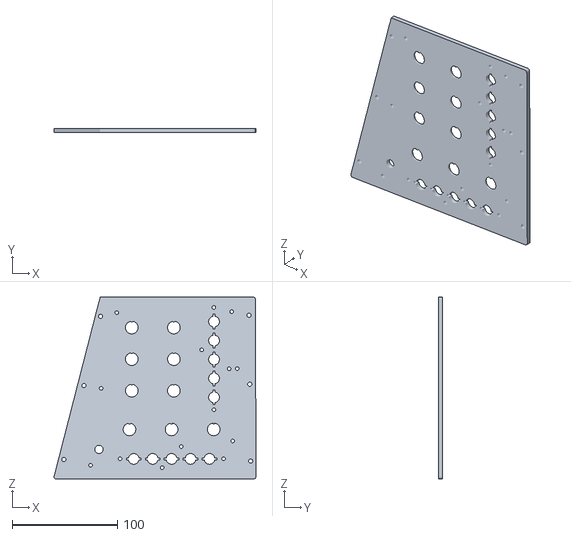
[picture p93: CAD file, 2025-04-07]
Panels/Right Vertical Panel/PDCP/PDCP - Bottom Panel.stl
191.9 x 4.00 x 172.9
