AHSolidSnake/F-14A-Cockpit/Panels/Support/Center Panel/ACM/ACM - Box - Bottom Left.stl

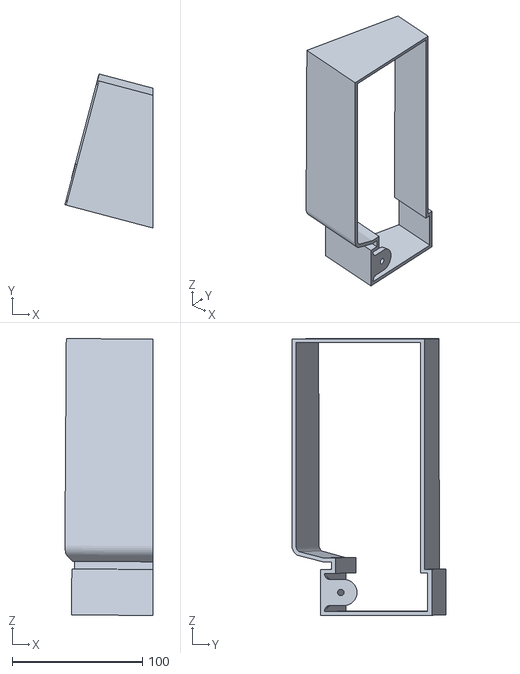
[picture p94: CAD file, 2025-03-09]
Panels/Support/Center Panel/ACM/ACM - Box - Bottom Left.stl
67.9 x 118.6 x 213.0
