AHSolidSnake/F-14A-Cockpit/Panels/Support/Center Panel/HSD/HSD - Box - Top.stl

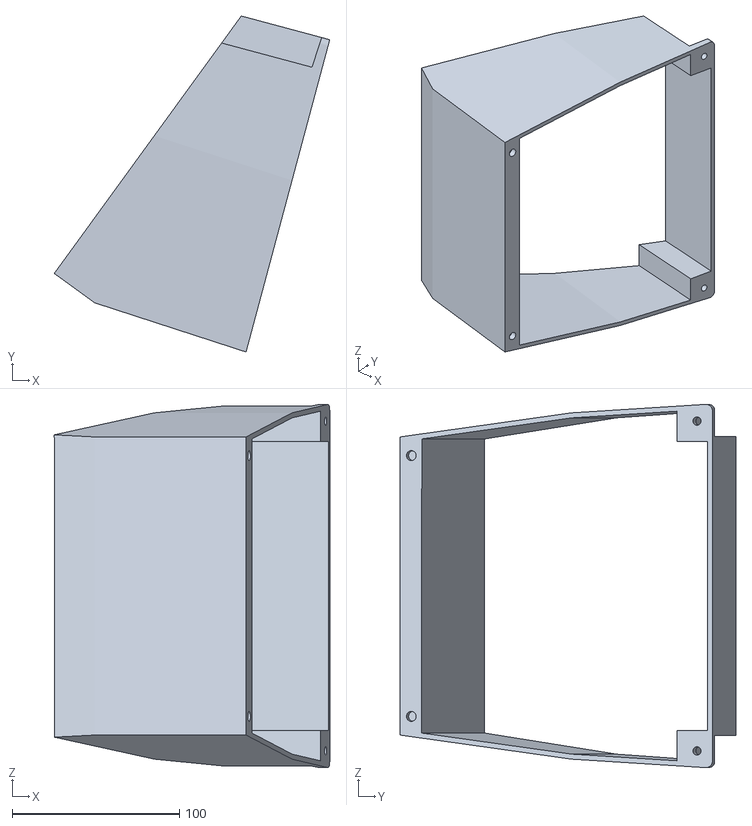
[picture p95: CAD file, 2025-03-30]
Panels/Support/Center Panel/HSD/HSD - Box - Top.stl
164.6 x 200.8 x 217.1
