AHSolidSnake/F-14A-Cockpit/Panels/Support/Center Panel/VDI/VDI - Box - Top.stl

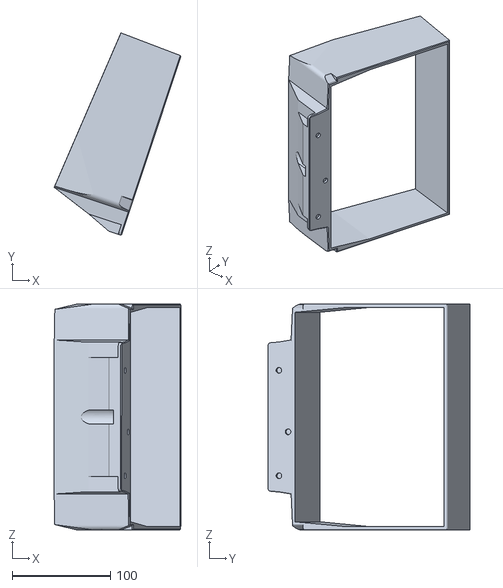
[picture p96: CAD file, 2025-03-29]
Panels/Support/Center Panel/VDI/VDI - Box - Top.stl
129.1 x 206.1 x 230.3
