AHSolidSnake/F-14A-Cockpit/Panels/Support/Left Vertical Panel/LVP - Box - Middle.stl

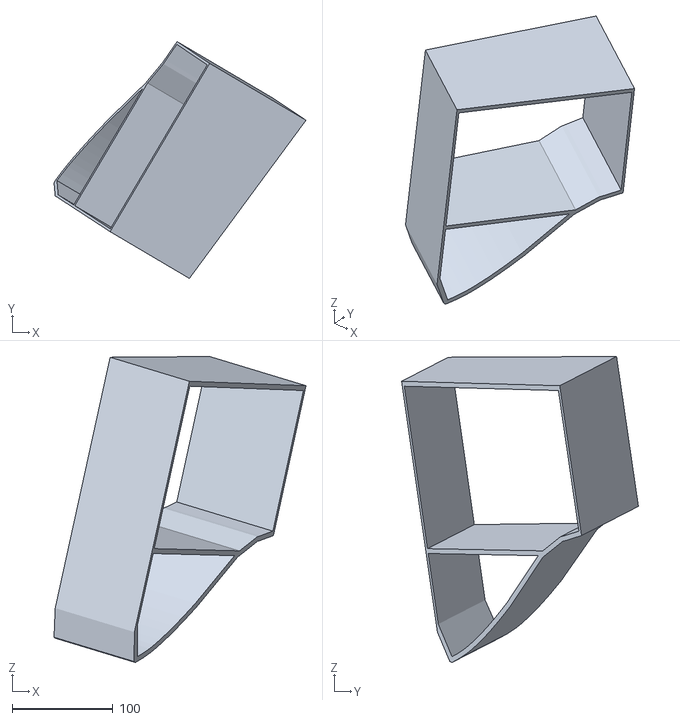
[picture p97: CAD file, 2025-03-30]
Panels/Support/Left Vertical Panel/LVP - Box - Middle.stl
250.0 x 235.0 x 303.6
