AHSolidSnake/F-14A-Cockpit/Panels/Support/Right Vertical Panel/RVP - Box - Top.stl

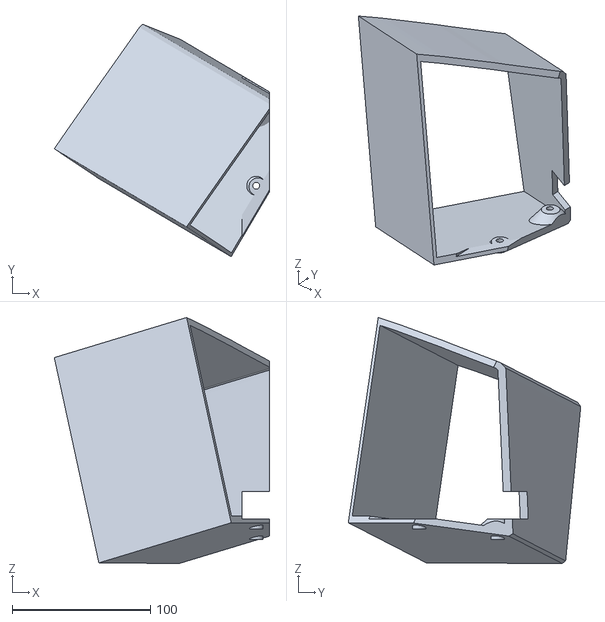
[picture p98: CAD file, 2025-03-30]
Panels/Support/Right Vertical Panel/RVP - Box - Top.stl
156.0 x 168.3 x 178.1
