AHSolidSnake/F-14A-Cockpit/Panels/Support/Side Panels/Left Front Wedge.stl

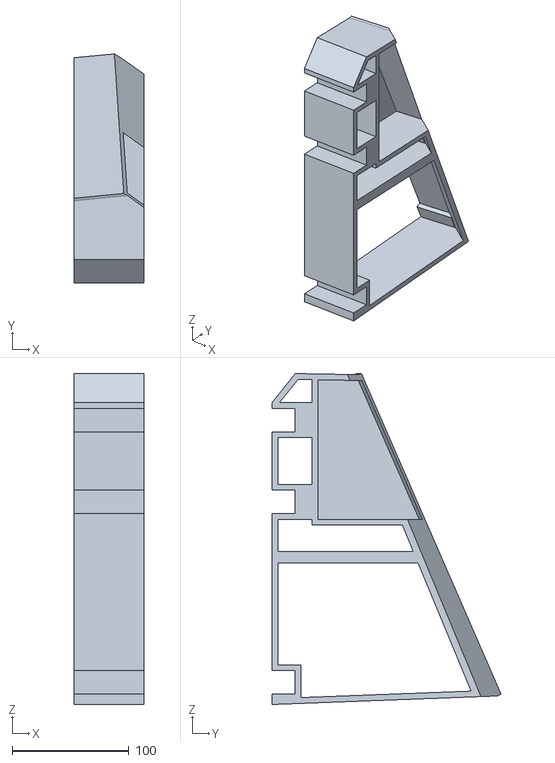
[picture p99: CAD file, 2025-06-24]
Panels/Support/Side Panels/Left Front Wedge.stl
60.0 x 196.7 x 284.1
