AHSolidSnake/F-14A-Cockpit/Throttle/Base/Box/Right Plate.step

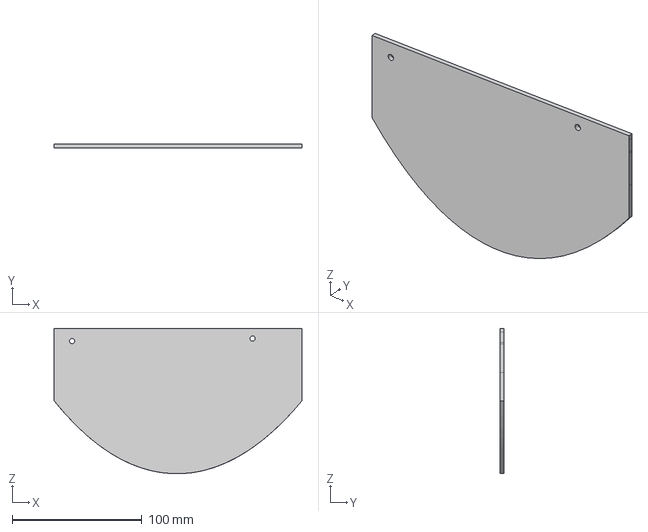
[picture p100: CAD file, 2025-05-17]
Throttle/Base/Box/Right Plate.step
191.0 x 3.00 x 111.9 mm
