AHSolidSnake/F-14A-Cockpit/Throttle/Base/Flaps/Flaps Cog.stl

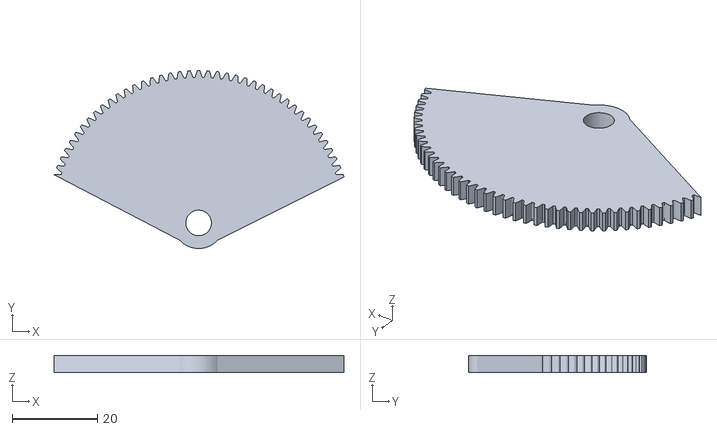
[picture p101: CAD file, 2025-06-24]
Throttle/Base/Flaps/Flaps Cog.stl
67.9 x 41.7 x 4.00
