AHSolidSnake/F-14A-Cockpit/Throttle/Base/Throttle Base/Throttle Levers Middle Left.stl

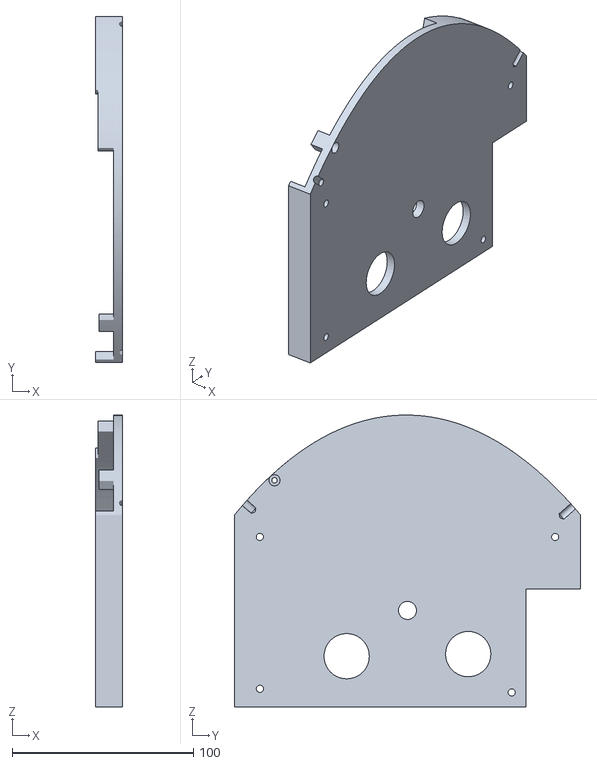
[picture p102: CAD file, 2025-06-24]
Throttle/Base/Throttle Base/Throttle Levers Middle Left.stl
15.0 x 191.0 x 161.1
