AHSolidSnake/F-14A-Cockpit/Throttle/Base/Wing Sweep/Wing Sweep Box.stl

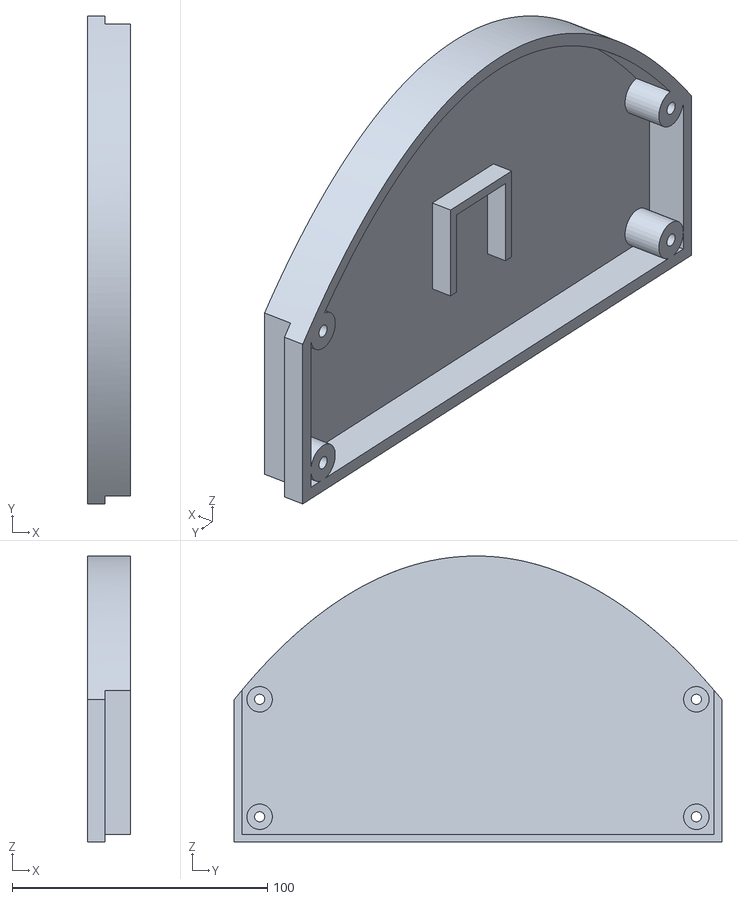
[picture p103: CAD file, 2025-06-24]
Throttle/Base/Wing Sweep/Wing Sweep Box.stl
17.0 x 191.0 x 112.0
