AHSolidSnake/F-14A-Cockpit/Throttle/Grips/Levers/Left Arm.stl

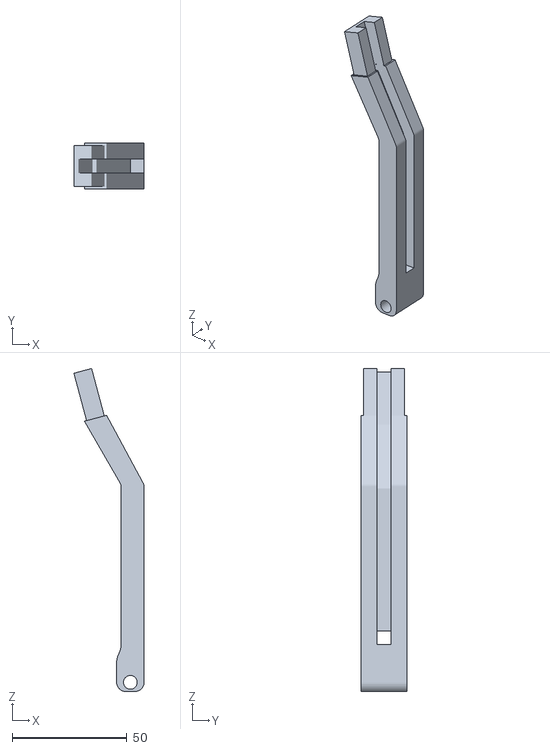
[picture p104: CAD file, 2025-06-24]
Throttle/Grips/Levers/Left Arm.stl
30.6 x 20.0 x 140.7
