AHSolidSnake/F-14A-Cockpit/Extras/BBI-32 Plate.stl

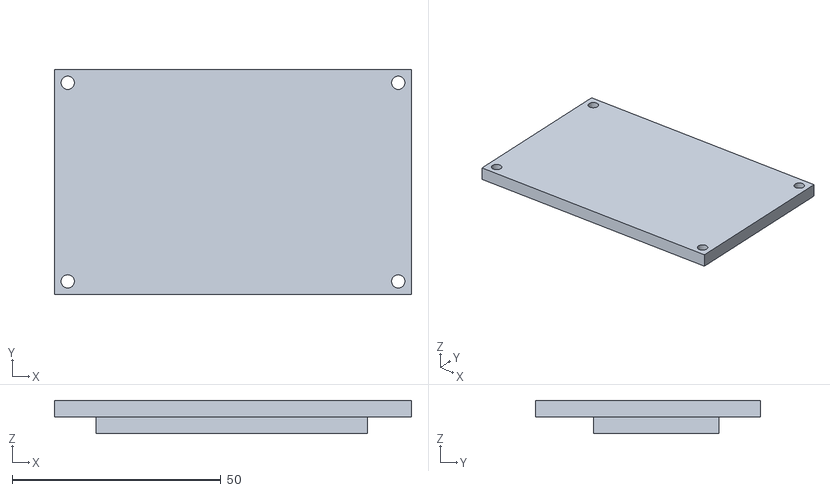
[picture p105: CAD file, 2025-03-23]
Extras/BBI-32 Plate.stl
85.6 x 54.0 x 8.00
