AHSolidSnake/F-14A-Cockpit/Panels/Center Panel/ACM/ACM - Lights/ACM - Lights - Hot Trig Light.stl

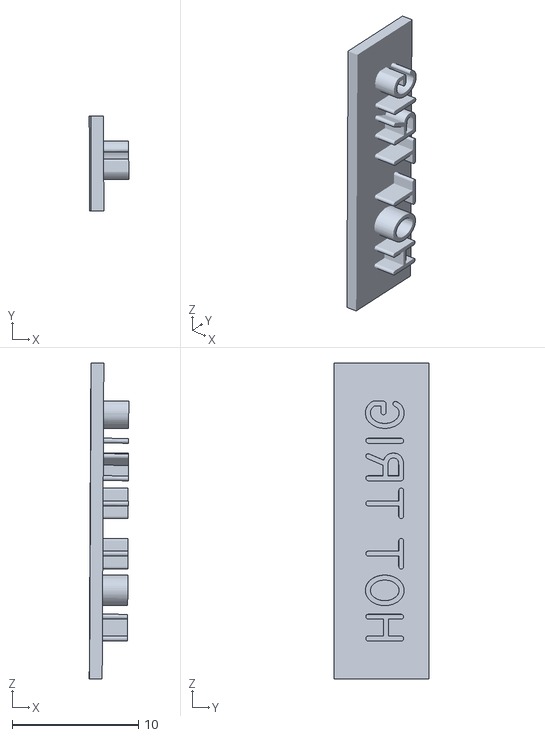
[picture p106: CAD file, 2025-03-16]
Panels/Center Panel/ACM/ACM - Lights/ACM - Lights - Hot Trig Light.stl
3.13 x 7.50 x 25.0
