AHSolidSnake/F-14A-Cockpit/Panels/Center Panel/ACM/ACM - Master Arm - Bracket.stl

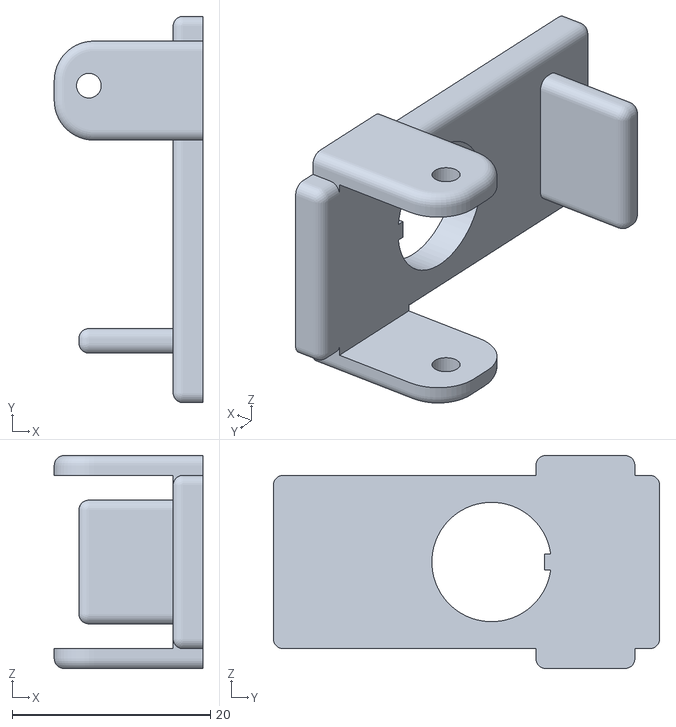
[picture p107: CAD file, 2025-03-16]
Panels/Center Panel/ACM/ACM - Master Arm - Bracket.stl
15.0 x 39.0 x 21.5
