AHSolidSnake/F-14A-Cockpit/Panels/Center Panel/VDI/VDI - Top Panel - Engrave.stl

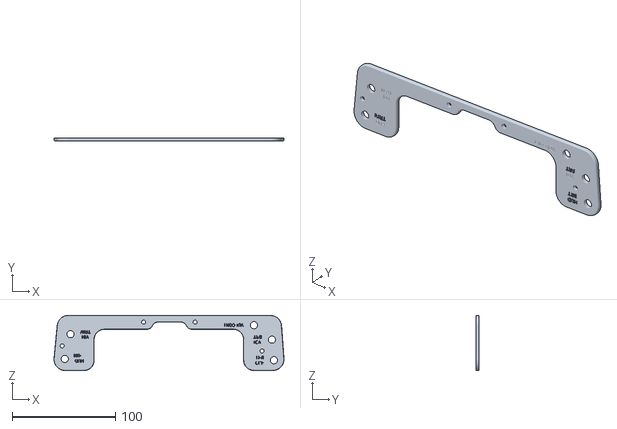
[picture p108: CAD file, 2025-03-29]
Panels/Center Panel/VDI/VDI - Top Panel - Engrave.stl
223.2 x 3.00 x 53.7
