AHSolidSnake/F-14A-Cockpit/Panels/Left Inboard/ARC-159/ARC-159 - Freq Cover.stl

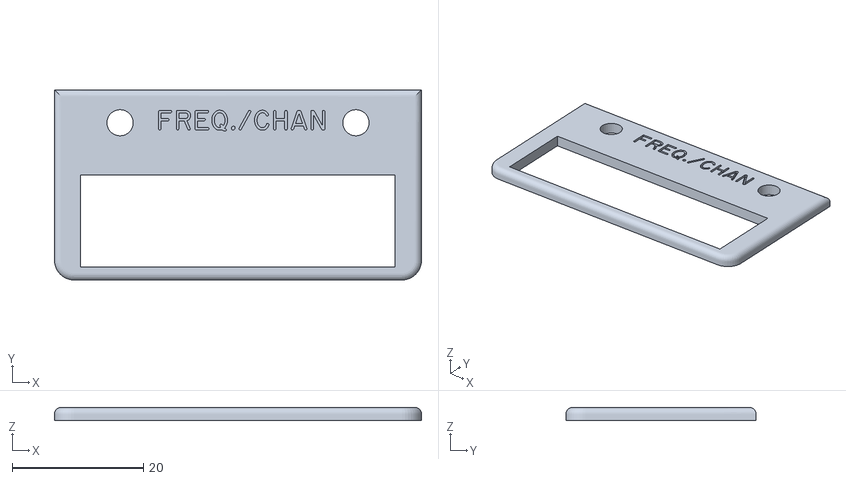
[picture p109: CAD file, 2025-07-18]
Panels/Left Inboard/ARC-159/ARC-159 - Freq Cover.stl
56.0 x 29.0 x 2.00
