AHSolidSnake/F-14A-Cockpit/Panels/Left Instrument Panel/Mach Meter.stl

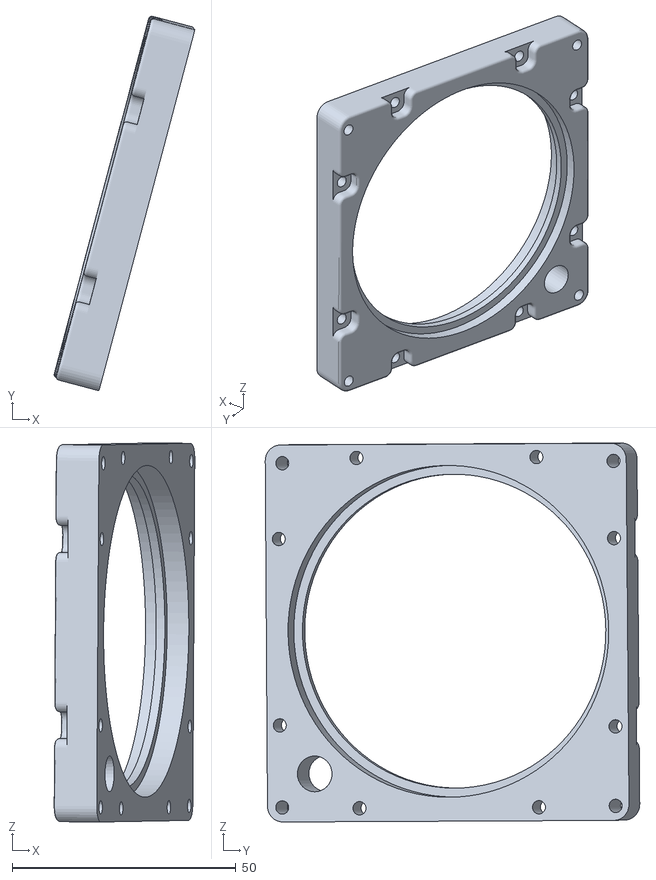
[picture p110: CAD file, 2025-03-30]
Panels/Left Instrument Panel/Mach Meter.stl
31.4 x 83.6 x 84.6
