AHSolidSnake/F-14A-Cockpit/Panels/Left Outboard/AFCS/AFCS - Bottom Panel.stl

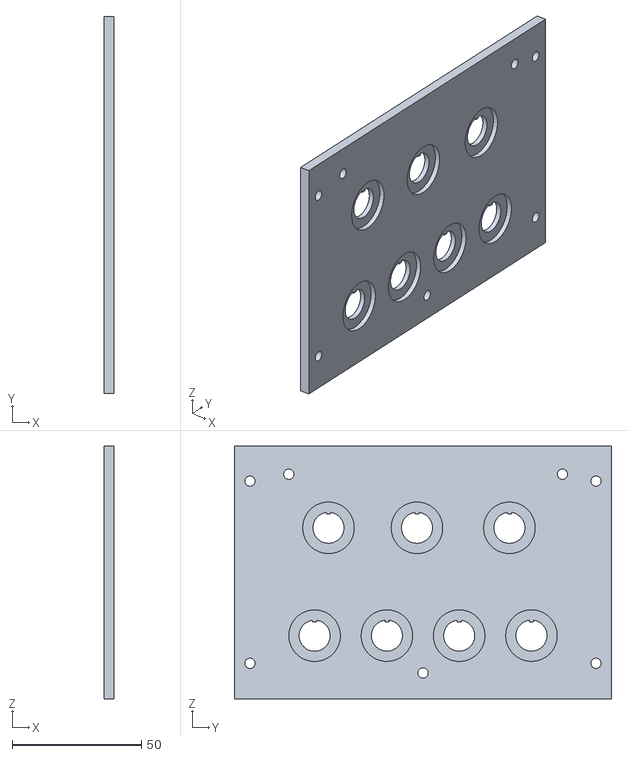
[picture p111: CAD file, 2025-02-09]
Panels/Left Outboard/AFCS/AFCS - Bottom Panel.stl
4.00 x 146.0 x 98.0
