AHSolidSnake/F-14A-Cockpit/Panels/Left Outboard/ASYM LIMIT/ASYM Limit - Bottom Panel.stl

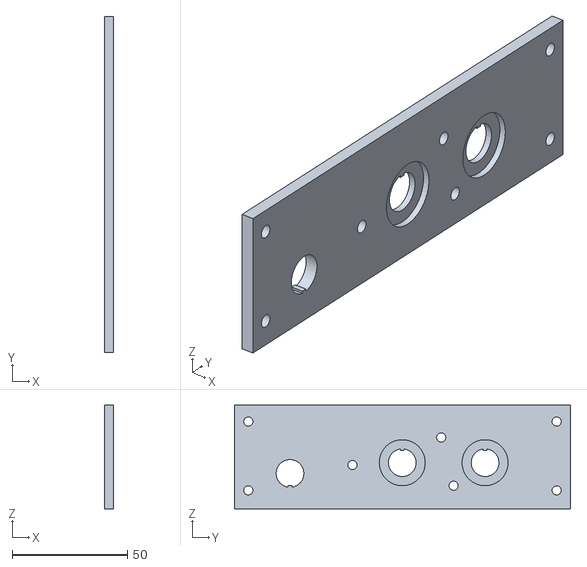
[picture p112: CAD file, 2025-02-13]
Panels/Left Outboard/ASYM LIMIT/ASYM Limit - Bottom Panel.stl
4.00 x 146.0 x 45.0
