AHSolidSnake/F-14A-Cockpit/Panels/Left Outboard/ICS/ICS - Bottom Panel.stl

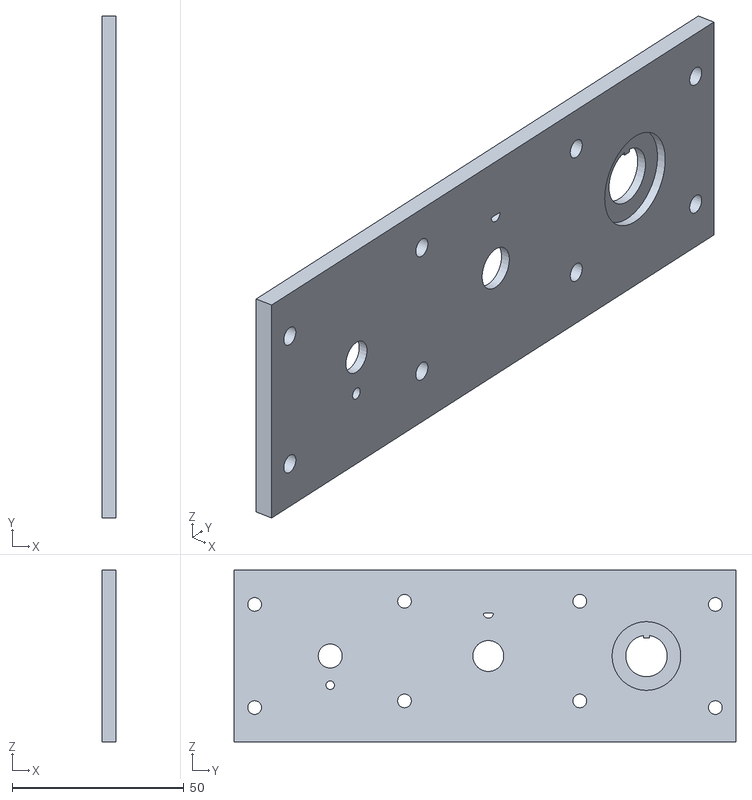
[picture p113: CAD file, 2025-02-09]
Panels/Left Outboard/ICS/ICS - Bottom Panel.stl
4.00 x 146.1 x 50.0
