AHSolidSnake/F-14A-Cockpit/Panels/Left Outboard/THROTTLE/THROTTLE - Bottom Panel.stl

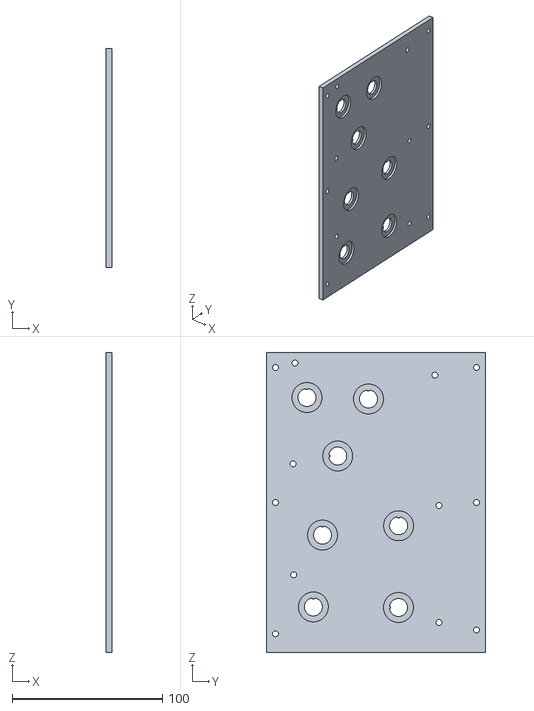
[picture p114: CAD file, 2025-02-09]
Panels/Left Outboard/THROTTLE/THROTTLE - Bottom Panel.stl
4.00 x 146.0 x 200.0
