AHSolidSnake/F-14A-Cockpit/Panels/Left Outboard/VOLUME/VOLUME - Bottom Panel.stl

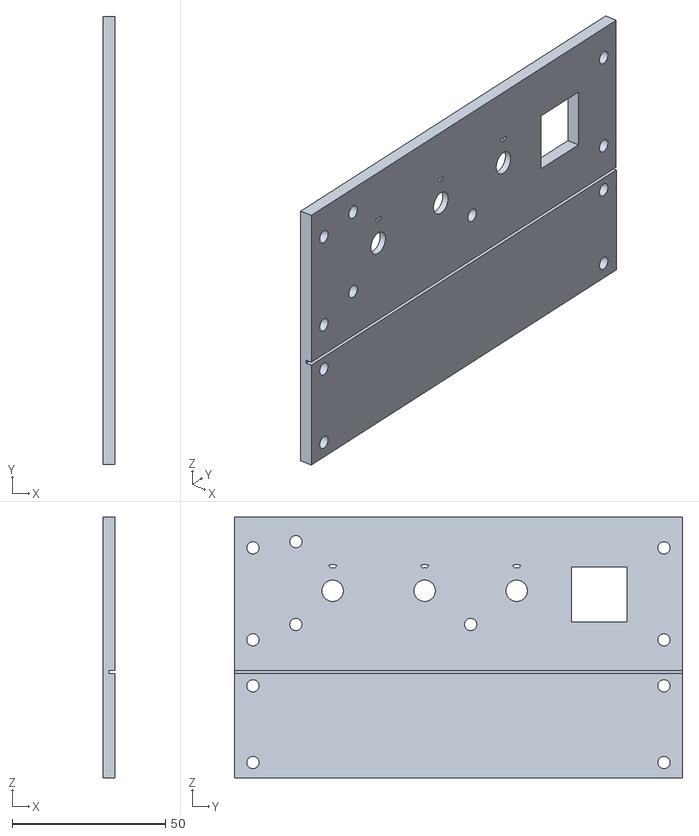
[picture p115: CAD file, 2025-02-09]
Panels/Left Outboard/VOLUME/VOLUME - Bottom Panel.stl
4.00 x 146.1 x 85.0
