AHSolidSnake/F-14A-Cockpit/Panels/Left Vertical Panel/FUEL/FUEL - Trim Window.stl

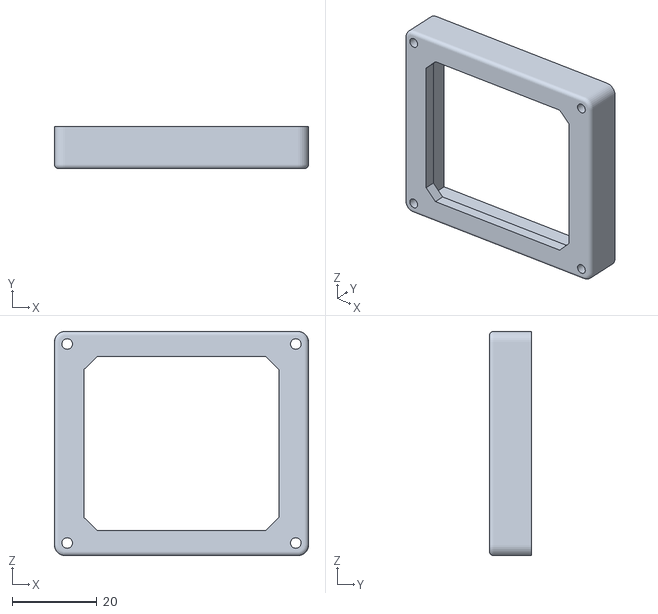
[picture p116: CAD file, 2025-03-23]
Panels/Left Vertical Panel/FUEL/FUEL - Trim Window.stl
60.0 x 10.0 x 53.0
