AHSolidSnake/F-14A-Cockpit/Panels/Left Vertical Panel/GEAR/GEAR - Handle.stl

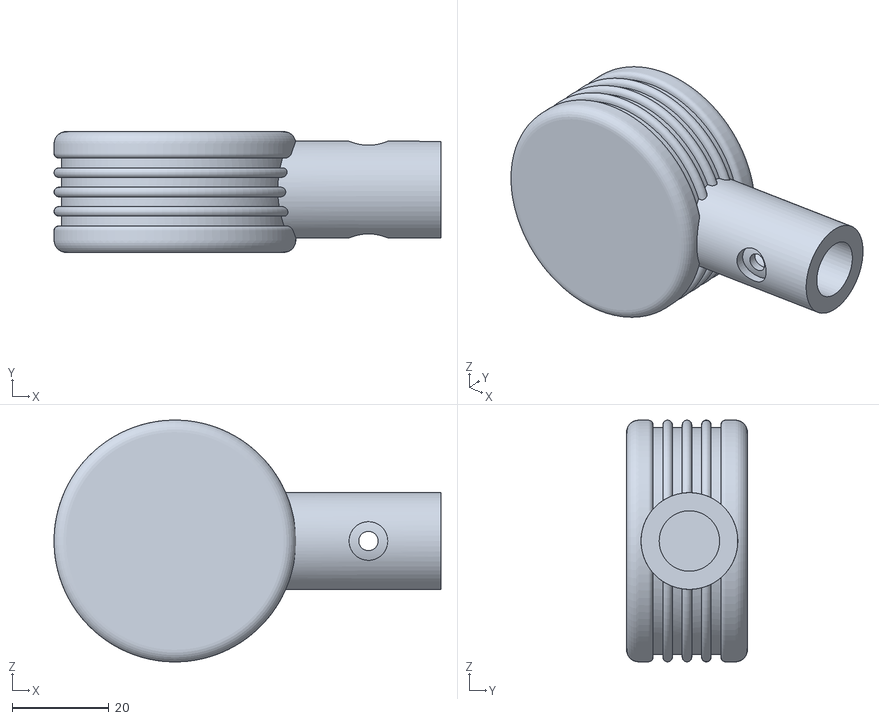
[picture p117: CAD file, 2025-06-24]
Panels/Left Vertical Panel/GEAR/GEAR - Handle.stl
80.0 x 25.0 x 50.0
