AHSolidSnake/F-14A-Cockpit/Panels/Right Inboard/AIRCON/AIRCON - Box.stl

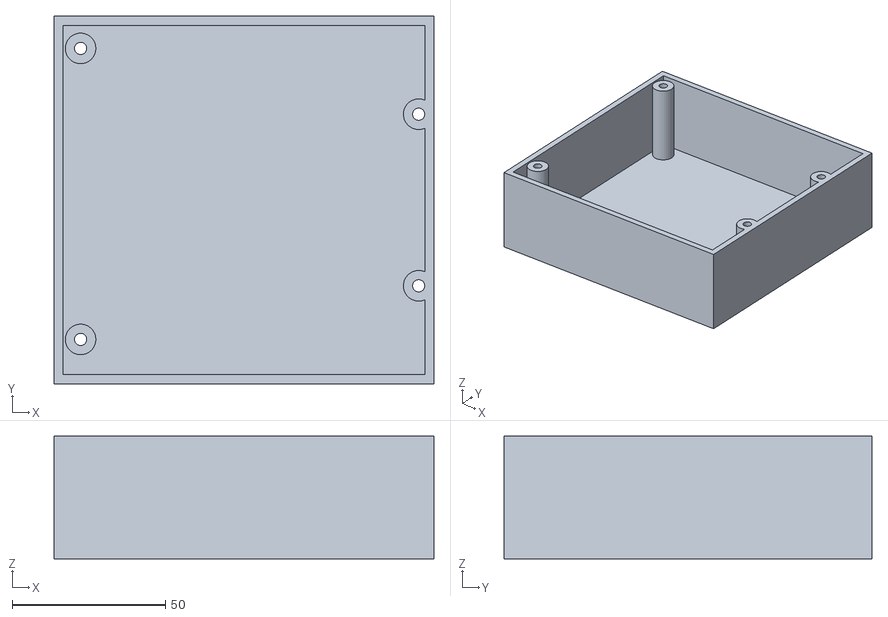
[picture p118: CAD file, 2025-04-28]
Panels/Right Inboard/AIRCON/AIRCON - Box.stl
124.1 x 120.0 x 40.0
