AHSolidSnake/F-14A-Cockpit/Panels/Right Inboard/C&W/C&W - Top Panel.stl

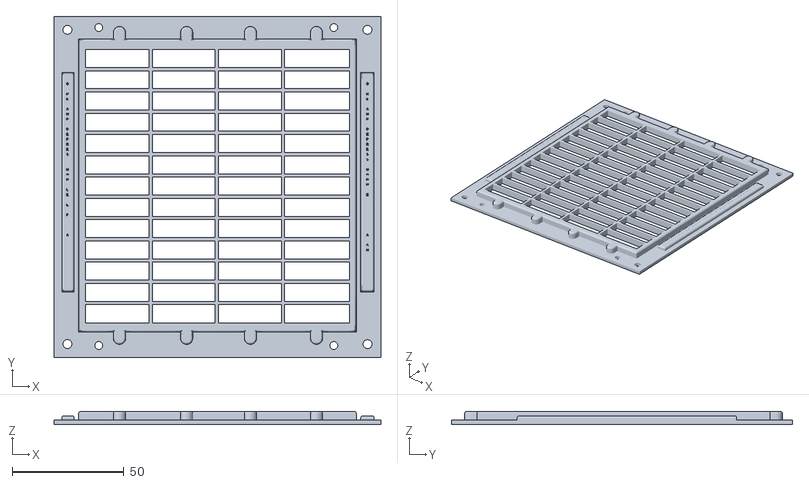
[picture p119: CAD file, 2025-03-30]
Panels/Right Inboard/C&W/C&W - Top Panel.stl
146.1 x 152.4 x 6.00
