AHSolidSnake/F-14A-Cockpit/Panels/Right Inboard/EXTENV/EXTENV - Bottom Panel.stl

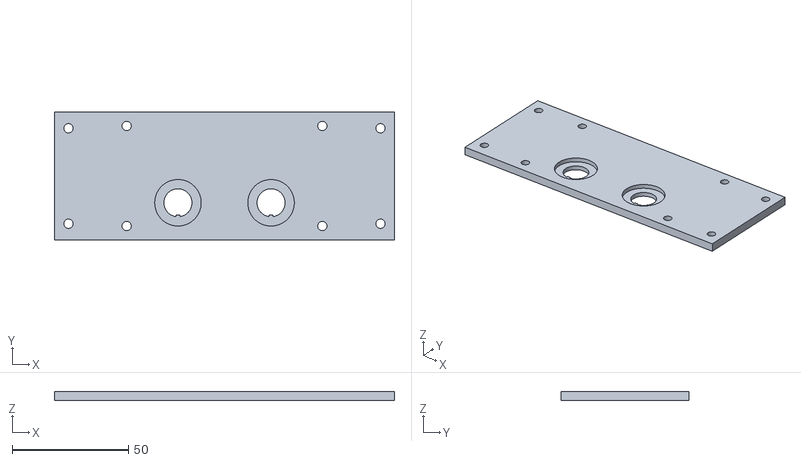
[picture p120: CAD file, 2025-04-13]
Panels/Right Inboard/EXTENV/EXTENV - Bottom Panel.stl
146.0 x 55.0 x 4.00
