AHSolidSnake/F-14A-Cockpit/Panels/Right Inboard/HYD TRANS/HYD TRANS - Top Panel - Engrave - Left.stl

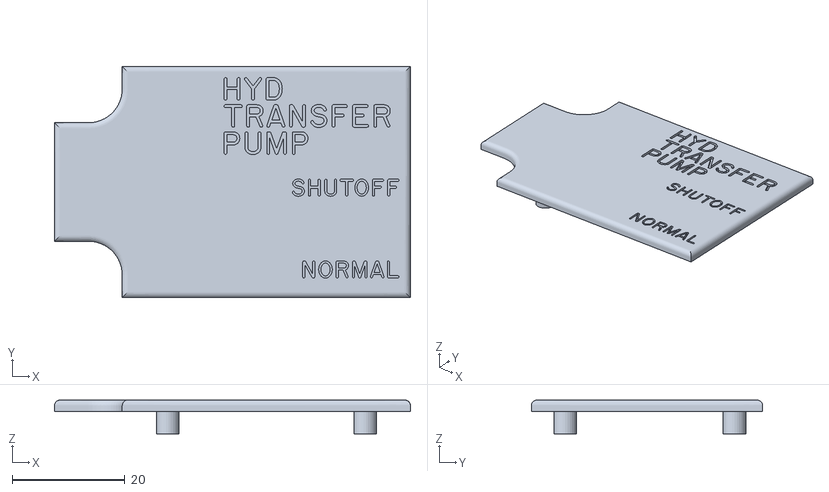
[picture p121: CAD file, 2025-03-30]
Panels/Right Inboard/HYD TRANS/HYD TRANS - Top Panel - Engrave - Left.stl
63.1 x 41.0 x 6.00
