AHSolidSnake/F-14A-Cockpit/Panels/Right Inboard/MASTERGEN/MASTERGEN - Top Panel - Light.stl

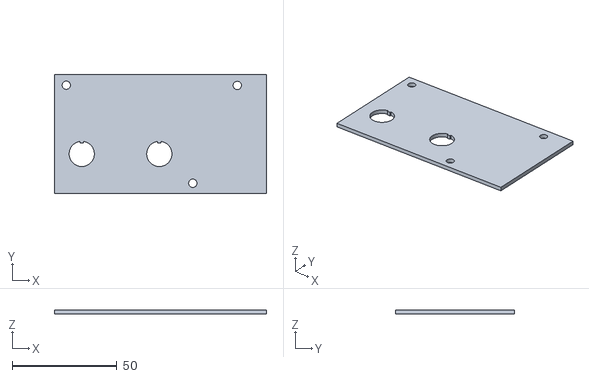
[picture p122: CAD file, 2025-03-30]
Panels/Right Inboard/MASTERGEN/MASTERGEN - Top Panel - Light.stl
101.1 x 57.0 x 2.00
