AHSolidSnake/F-14A-Cockpit/Panels/Right Instrument Panel/Landing checklist back.3mf

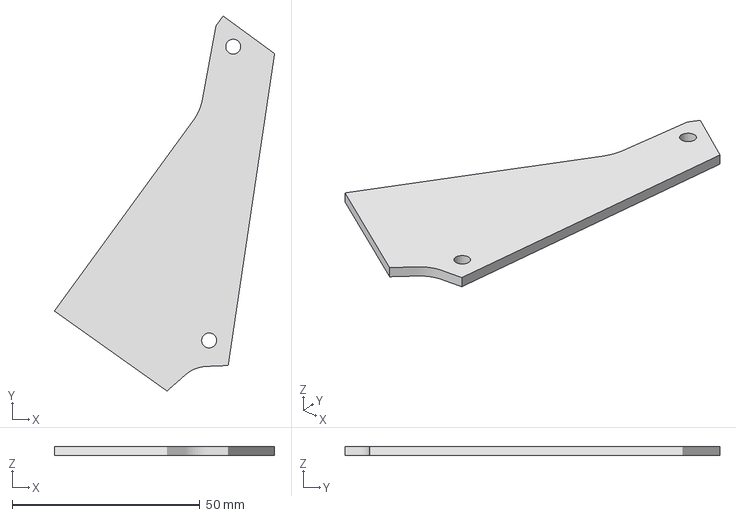
[picture p123: CAD file, 2025-03-30]
Panels/Right Instrument Panel/Landing checklist back.3mf
58.7 x 99.9 x 2.50 mm
