AHSolidSnake/F-14A-Cockpit/Panels/Right Outboard/COMPASS/COMPASS - Top Panel - Light.stl

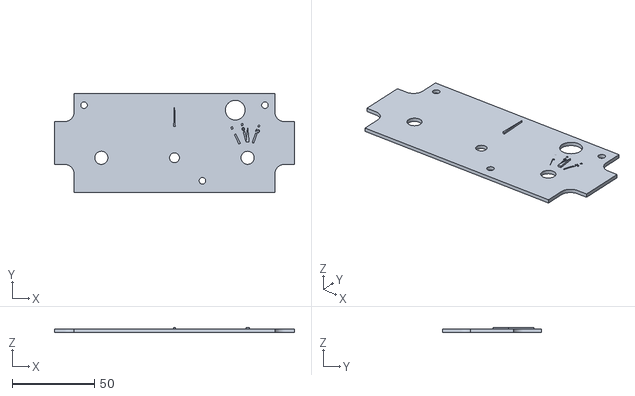
[picture p124: CAD file, 2025-03-30]
Panels/Right Outboard/COMPASS/COMPASS - Top Panel - Light.stl
146.1 x 60.0 x 3.00
