AHSolidSnake/F-14A-Cockpit/Panels/Right Outboard/ILS/ILS - Top Panel.stl

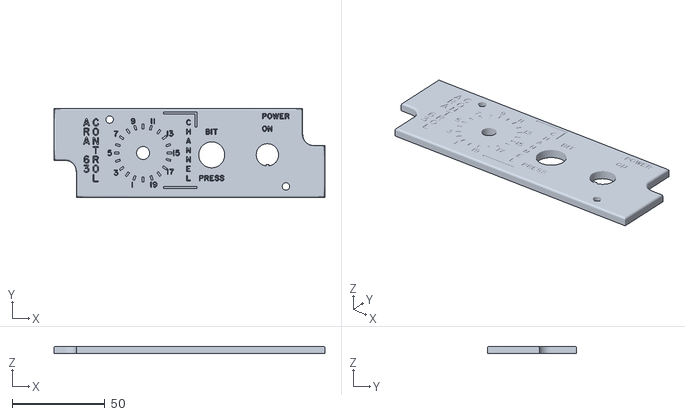
[picture p125: CAD file, 2025-03-30]
Panels/Right Outboard/ILS/ILS - Top Panel.stl
146.1 x 48.0 x 4.00
