AHSolidSnake/F-14A-Cockpit/Panels/Right Outboard/MASTER LIGHTS/MASTER LIGHTS - Top Panel - Light.stl

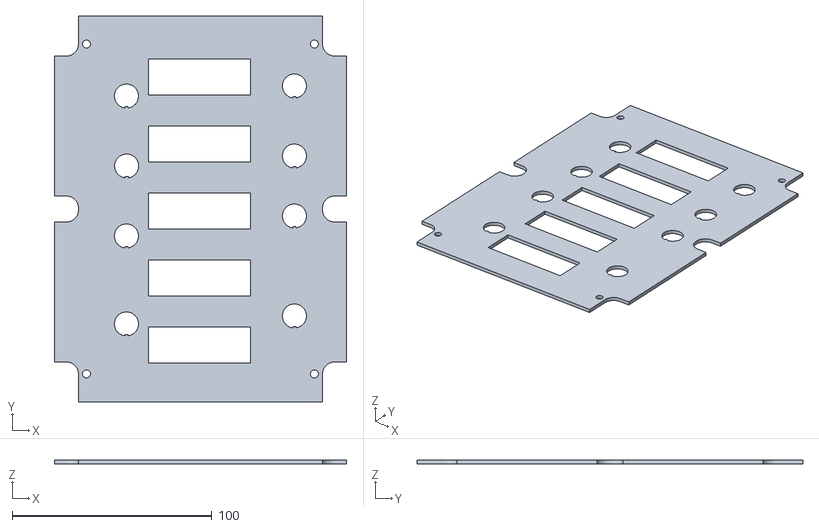
[picture p126: CAD file, 2025-03-30]
Panels/Right Outboard/MASTER LIGHTS/MASTER LIGHTS - Top Panel - Light.stl
146.1 x 193.0 x 2.00
