AHSolidSnake/F-14A-Cockpit/Panels/Right Outboard/MASTER TEST/MASTER TEST - Box.stl

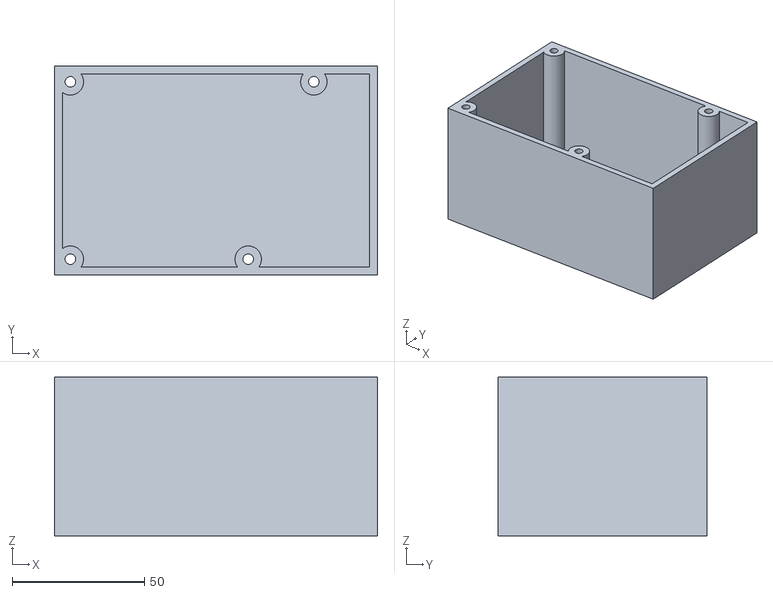
[picture p127: CAD file, 2025-03-30]
Panels/Right Outboard/MASTER TEST/MASTER TEST - Box.stl
122.0 x 79.0 x 60.0
