AHSolidSnake/F-14A-Cockpit/Panels/Right Sidewall/CANOPY/CANOPY - Panel.stl

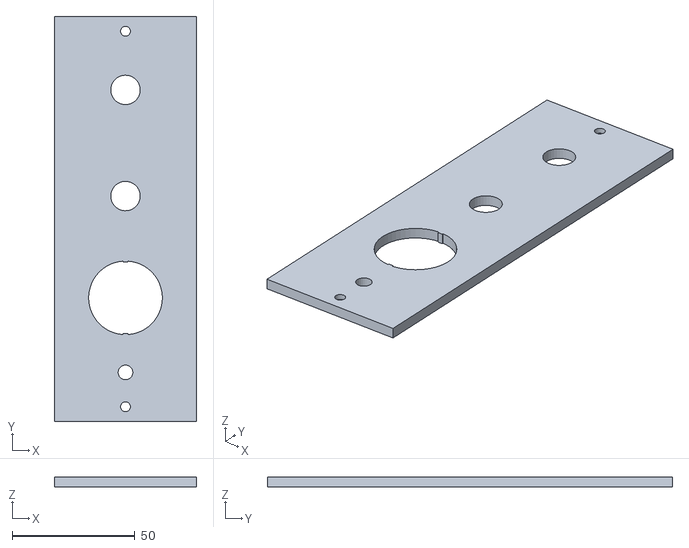
[picture p128: CAD file, 2025-06-24]
Panels/Right Sidewall/CANOPY/CANOPY - Panel.stl
58.0 x 165.0 x 4.00
