AHSolidSnake/F-14A-Cockpit/Panels/Right Vertical Panel/ELEV LEAD/ELEV LEAD - Bottom Panel.stl

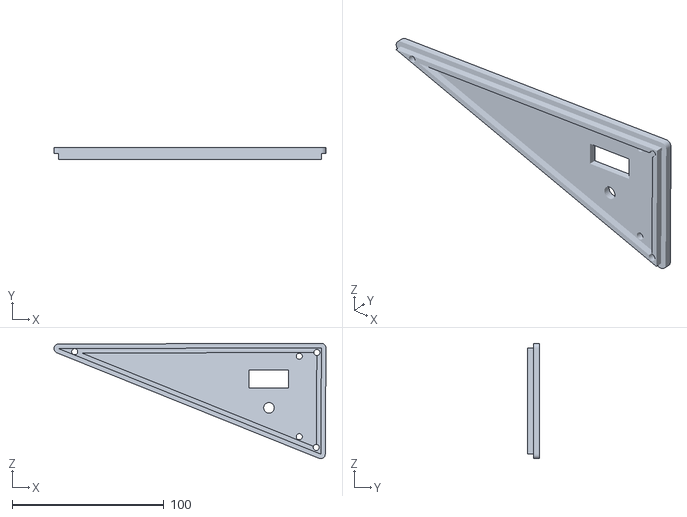
[picture p129: CAD file, 2025-04-11]
Panels/Right Vertical Panel/ELEV LEAD/ELEV LEAD - Bottom Panel.stl
179.2 x 8.00 x 76.0
