AHSolidSnake/F-14A-Cockpit/Panels/Right Vertical Panel/HOOK/HOOK - Rounds Counter - Base.stl

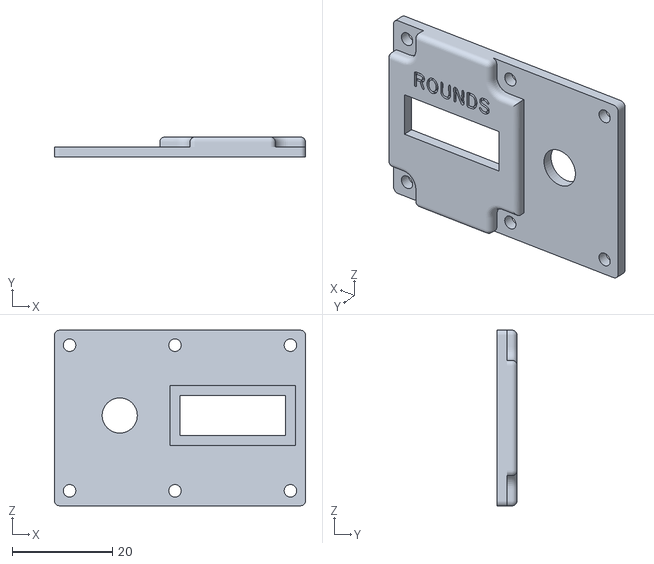
[picture p130: CAD file, 2025-04-29]
Panels/Right Vertical Panel/HOOK/HOOK - Rounds Counter - Base.stl
50.0 x 4.00 x 35.0
