AHSolidSnake/F-14A-Cockpit/Panels/Right Vertical Panel/PDCP/PDCP - Top Panel - Light.stl

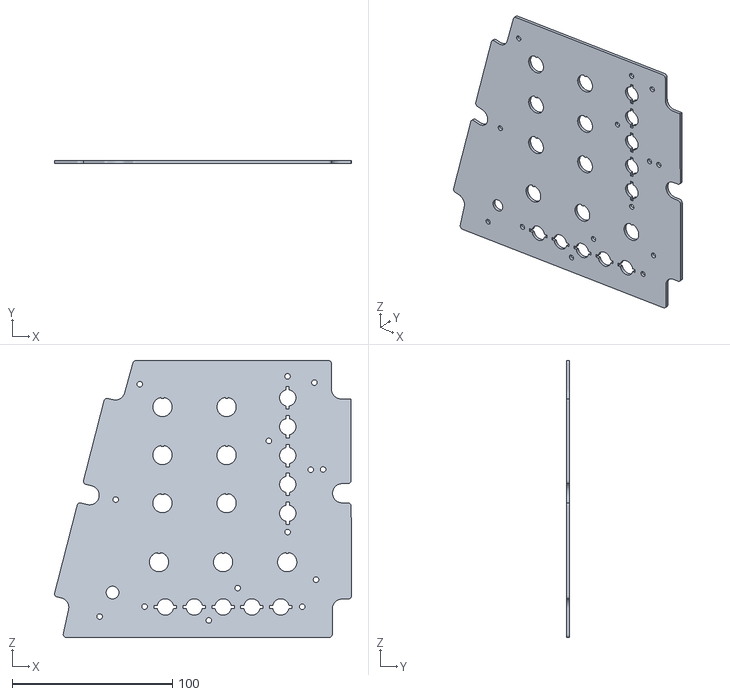
[picture p131: CAD file, 2025-04-07]
Panels/Right Vertical Panel/PDCP/PDCP - Top Panel - Light.stl
185.3 x 2.00 x 172.9
