AHSolidSnake/F-14A-Cockpit/Panels/Support/Center Panel/ACM/ACM - Box - Bottom Right.stl

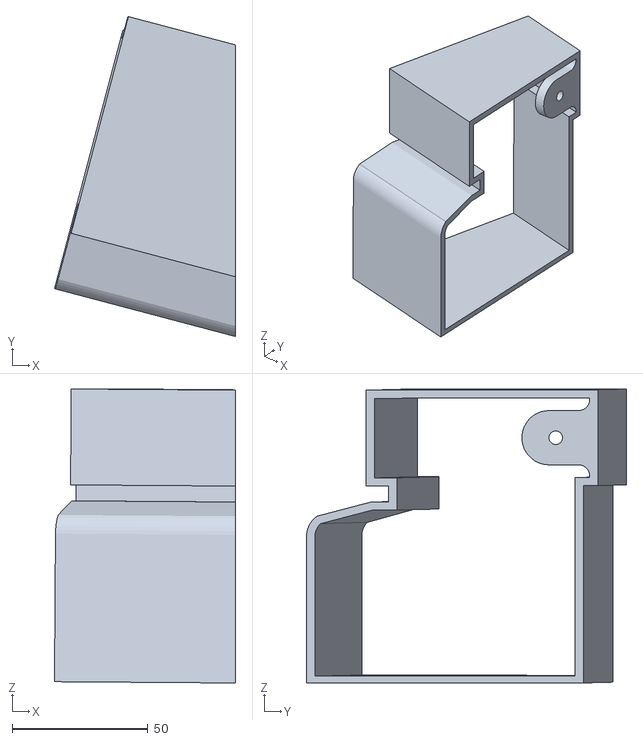
[picture p132: CAD file, 2025-03-09]
Panels/Support/Center Panel/ACM/ACM - Box - Bottom Right.stl
66.8 x 118.1 x 108.4
