AHSolidSnake/F-14A-Cockpit/Panels/Support/Right Vertical Panel/RVP - Box - Middle.stl

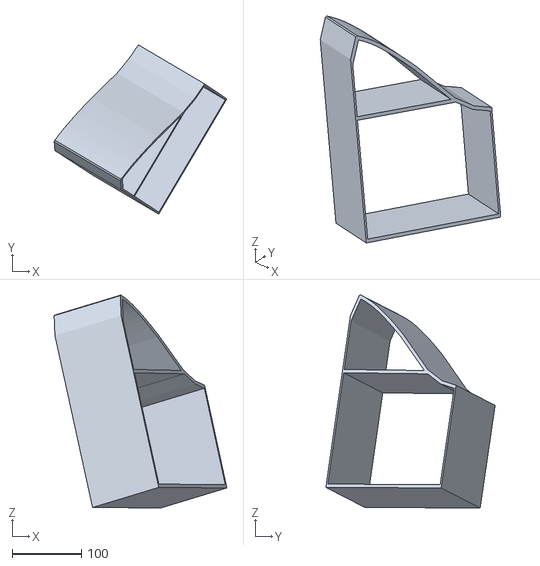
[picture p133: CAD file, 2025-03-30]
Panels/Support/Right Vertical Panel/RVP - Box - Middle.stl
250.2 x 245.1 x 308.5
