AHSolidSnake/F-14A-Cockpit/Panels/Support/Side Panels/Left Back Wedge.stl

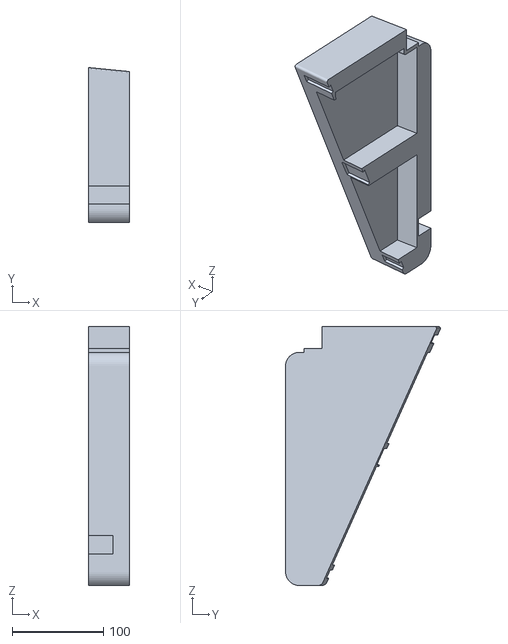
[picture p134: CAD file, 2025-04-28]
Panels/Support/Side Panels/Left Back Wedge.stl
44.5 x 169.9 x 283.9
