AHSolidSnake/F-14A-Cockpit/Throttle/Base/Box/Front-Back Plate.step

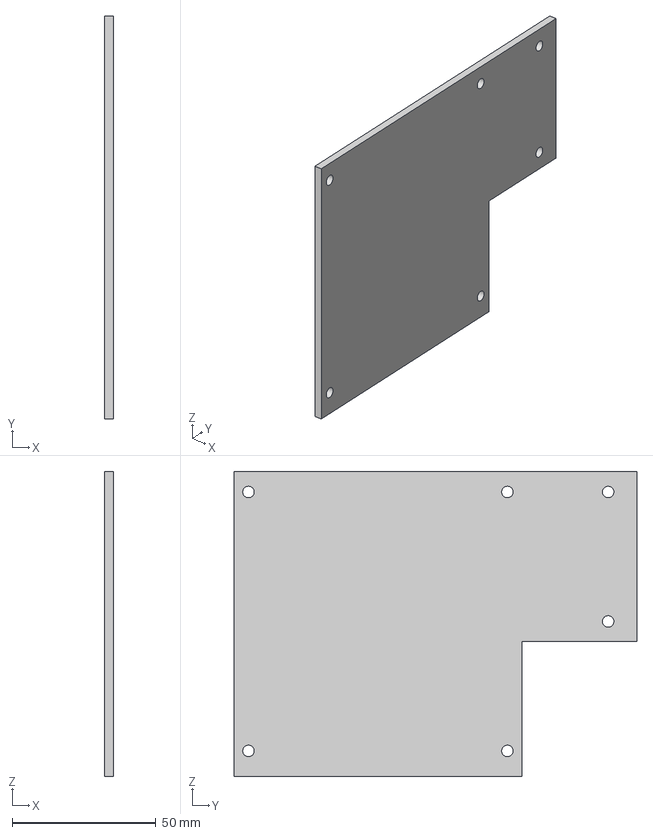
[picture p135: CAD file, 2025-05-17]
Throttle/Base/Box/Front-Back Plate.step
3.00 x 140.0 x 106.0 mm
