AHSolidSnake/F-14A-Cockpit/Throttle/Base/Wing Sweep/Wing Sweep Tab.stl

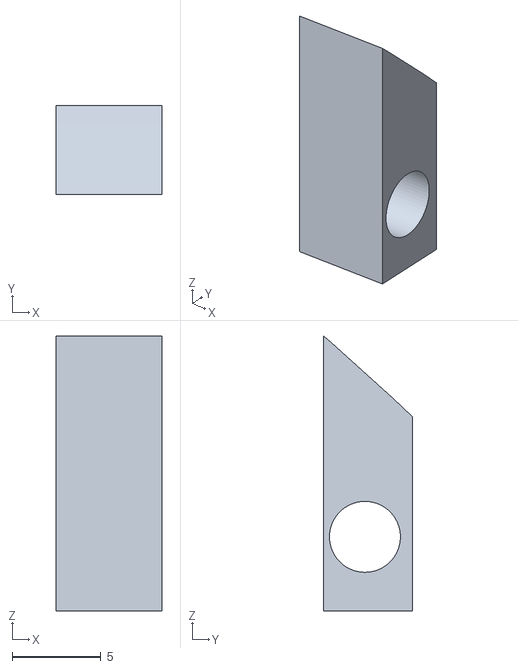
[picture p136: CAD file, 2025-06-24]
Throttle/Base/Wing Sweep/Wing Sweep Tab.stl
6.00 x 5.00 x 15.5
