AHSolidSnake/F-14A-Cockpit/Throttle/Grips/Levers/Right Lever Boot.stl

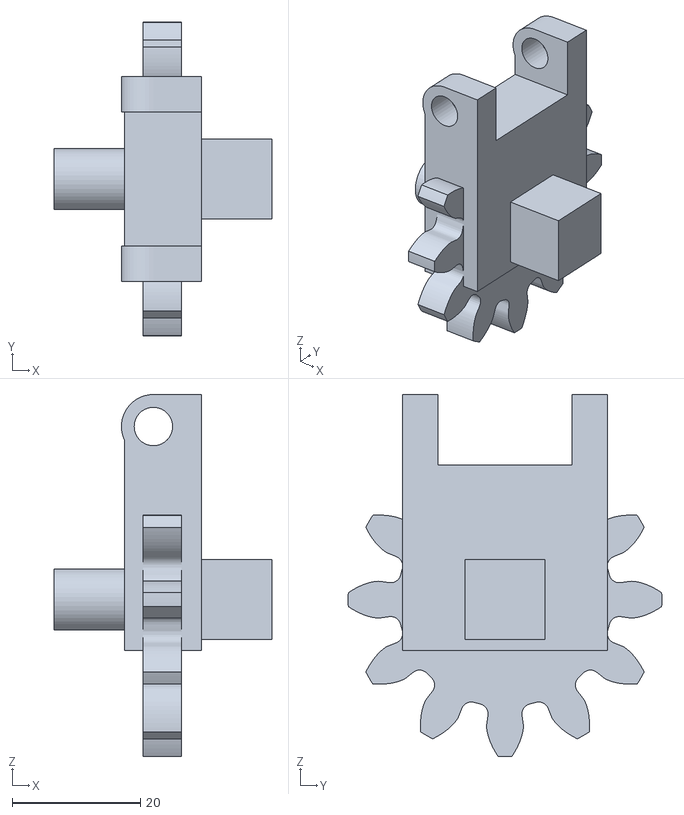
[picture p137: CAD file, 2025-06-24]
Throttle/Grips/Levers/Right Lever Boot.stl
34.0 x 49.0 x 56.5
