AHSolidSnake/F-14A-Cockpit/Extras/USB Plug x2.stl

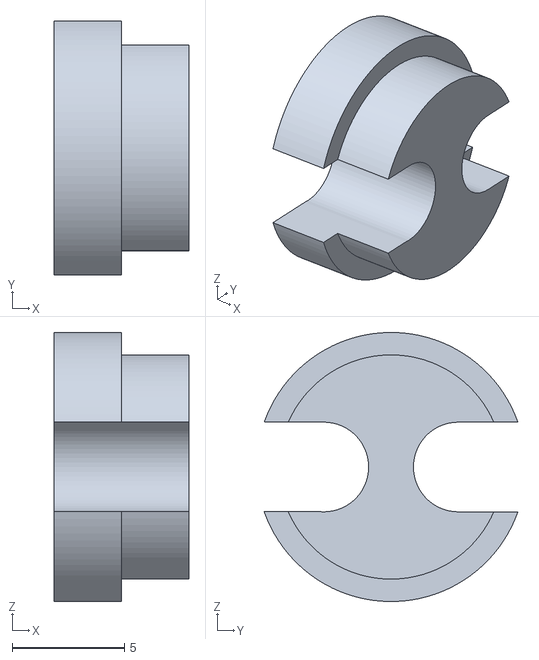
[picture p138: CAD file, 2025-02-14]
Extras/USB Plug x2.stl
6.00 x 11.3 x 12.0
