AHSolidSnake/F-14A-Cockpit/Panels/Center Panel/ACM/ACM - Back Panel.stl

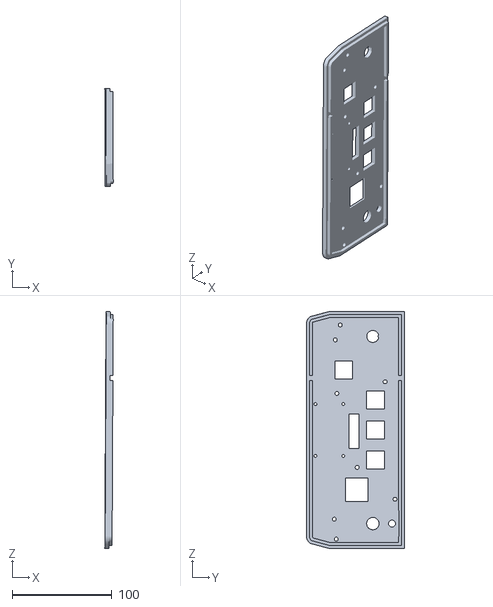
[picture p139: CAD file, 2025-03-09]
Panels/Center Panel/ACM/ACM - Back Panel.stl
8.54 x 98.8 x 238.0
