AHSolidSnake/F-14A-Cockpit/Panels/Center Panel/ACM/ACM - Lights/ACM - Lights - SEAM Light.stl

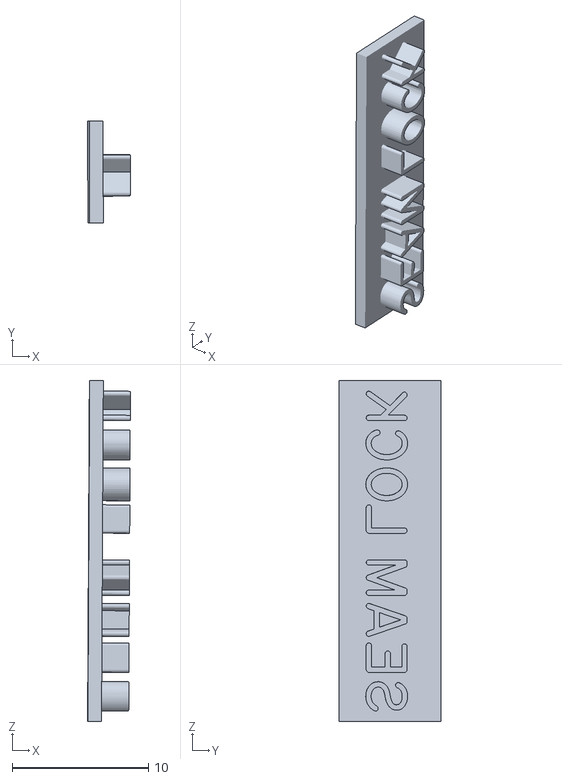
[picture p140: CAD file, 2025-03-16]
Panels/Center Panel/ACM/ACM - Lights/ACM - Lights - SEAM Light.stl
3.15 x 7.50 x 25.0
