AHSolidSnake/F-14A-Cockpit/Panels/Left Inboard/ARC-159/ARC-159 - Bottom Panel.stl

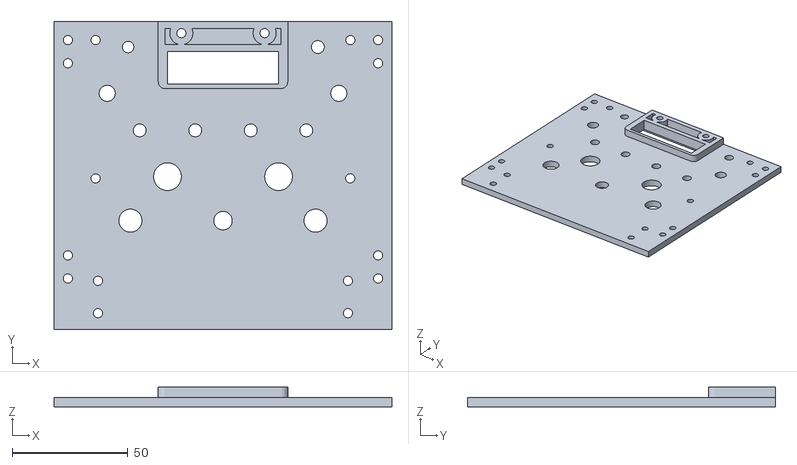
[picture p141: CAD file, 2025-07-18]
Panels/Left Inboard/ARC-159/ARC-159 - Bottom Panel.stl
146.1 x 133.0 x 8.50
