AHSolidSnake/F-14A-Cockpit/Panels/Left Outboard/AFCS/AFCS - Box.stl

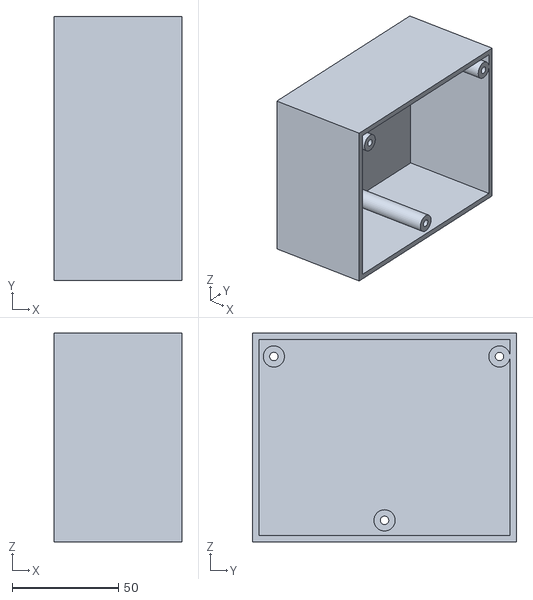
[picture p143: CAD file, 2025-02-09]
Panels/Left Outboard/AFCS/AFCS - Box.stl
60.0 x 124.0 x 98.0
