AHSolidSnake/F-14A-Cockpit/Panels/Left Outboard/ASYM LIMIT/ASYM Limit - Box.stl

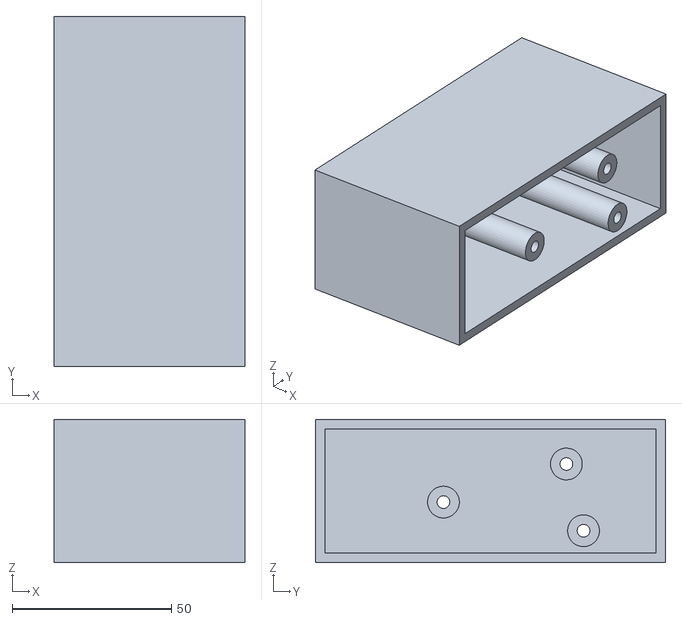
[picture p144: CAD file, 2025-02-09]
Panels/Left Outboard/ASYM LIMIT/ASYM Limit - Box.stl
60.0 x 110.0 x 45.0
