AHSolidSnake/F-14A-Cockpit/Panels/Left Outboard/ICS/ICS - Box.stl

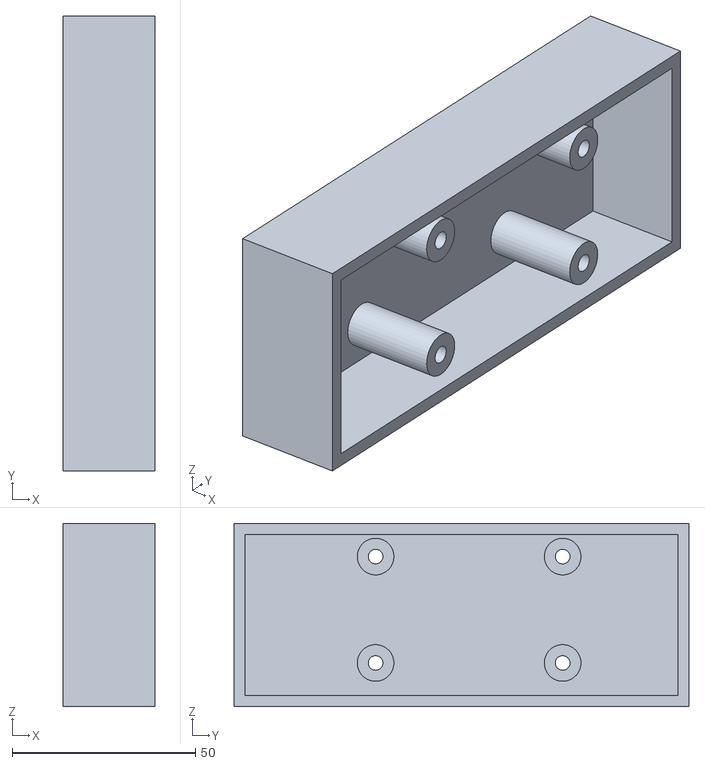
[picture p145: CAD file, 2025-02-09]
Panels/Left Outboard/ICS/ICS - Box.stl
25.0 x 124.1 x 50.0
