AHSolidSnake/F-14A-Cockpit/Panels/Left Outboard/THROTTLE/THROTTLE - Box.stl

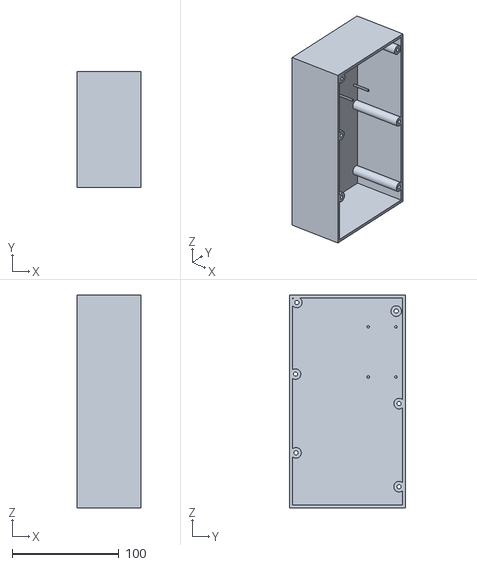
[picture p146: CAD file, 2025-02-09]
Panels/Left Outboard/THROTTLE/THROTTLE - Box.stl
60.0 x 109.0 x 200.0
