AHSolidSnake/F-14A-Cockpit/Panels/Left Outboard/VOLUME/VOLUME - Box.stl

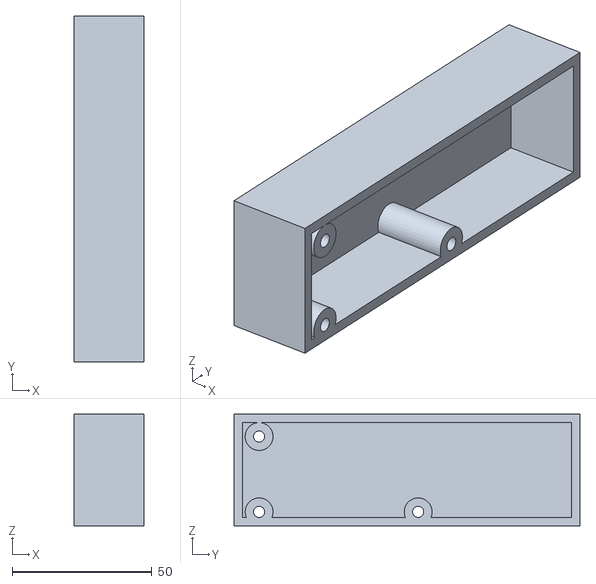
[picture p147: CAD file, 2025-02-09]
Panels/Left Outboard/VOLUME/VOLUME - Box.stl
25.0 x 124.0 x 40.0
