AHSolidSnake/F-14A-Cockpit/Panels/Left Vertical Panel/FUEL/FUEL - Trim Instruments.stl

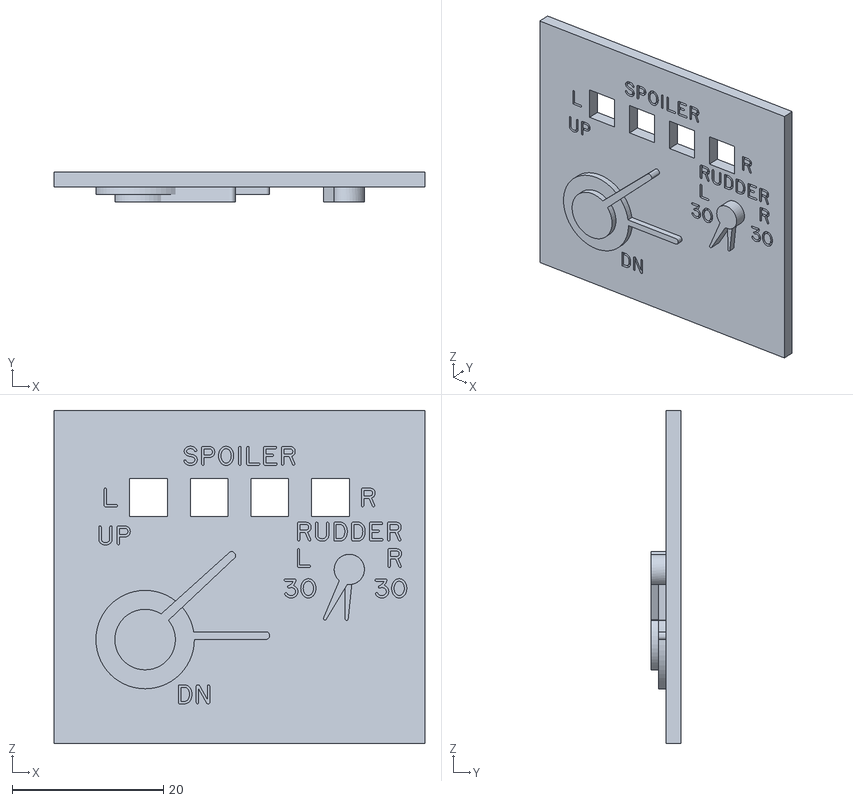
[picture p148: CAD file, 2025-03-23]
Panels/Left Vertical Panel/FUEL/FUEL - Trim Instruments.stl
49.0 x 4.00 x 44.0
