AHSolidSnake/F-14A-Cockpit/Panels/Right Inboard/AIRCON/AIRCON - Top Panel - Engrave.stl

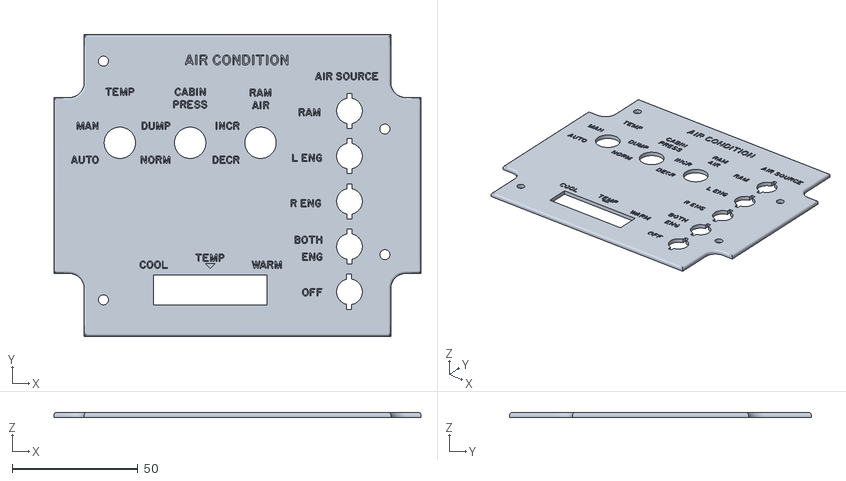
[picture p149: CAD file, 2025-04-07]
Panels/Right Inboard/AIRCON/AIRCON - Top Panel - Engrave.stl
146.0 x 120.0 x 2.00
