AHSolidSnake/F-14A-Cockpit/Panels/Right Inboard/EXTENV/EXTENV - Top Panel - Light.stl

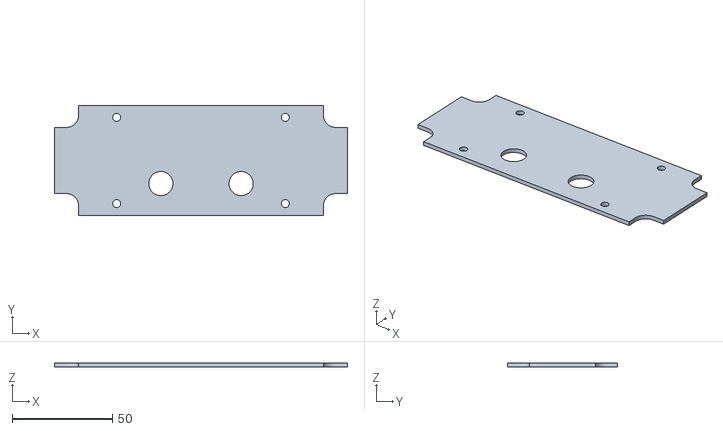
[picture p151: CAD file, 2025-04-13]
Panels/Right Inboard/EXTENV/EXTENV - Top Panel - Light.stl
146.0 x 55.0 x 2.00
