AHSolidSnake/F-14A-Cockpit/Panels/Right Inboard/HYD TRANS/HYD TRANS - Top Panel - Right.stl

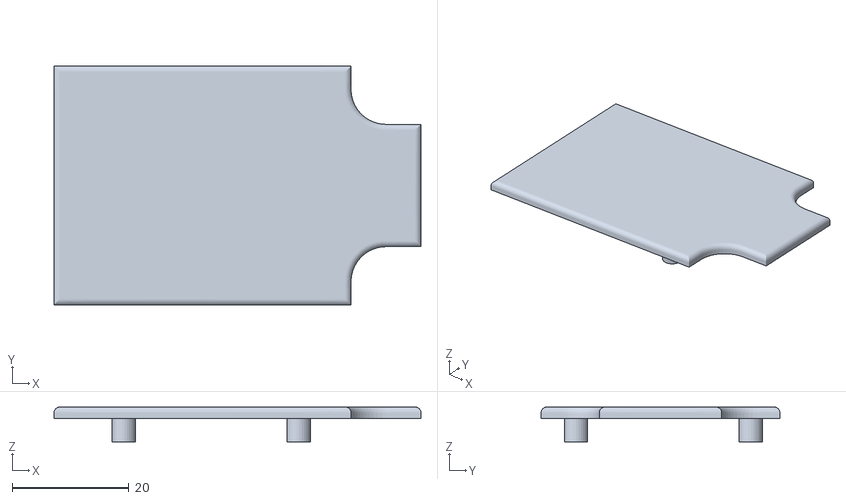
[picture p152: CAD file, 2025-03-30]
Panels/Right Inboard/HYD TRANS/HYD TRANS - Top Panel - Right.stl
63.0 x 41.0 x 6.00
